serge-scl/mini-keyboard/part/wheell_z2_2.FCStd

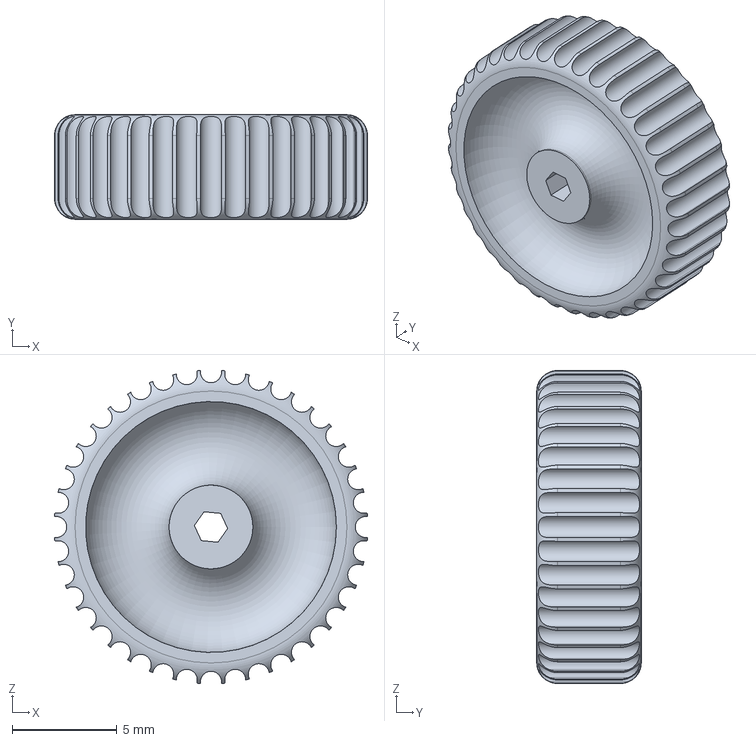
[picture p18: CAD file, 2025-04-07]
part/wheell_z2_2.FCStd
15.0 x 5.00 x 15.0 mm
