serge-scl/mini-keyboard/assembly/plug_front_conn.FCStd

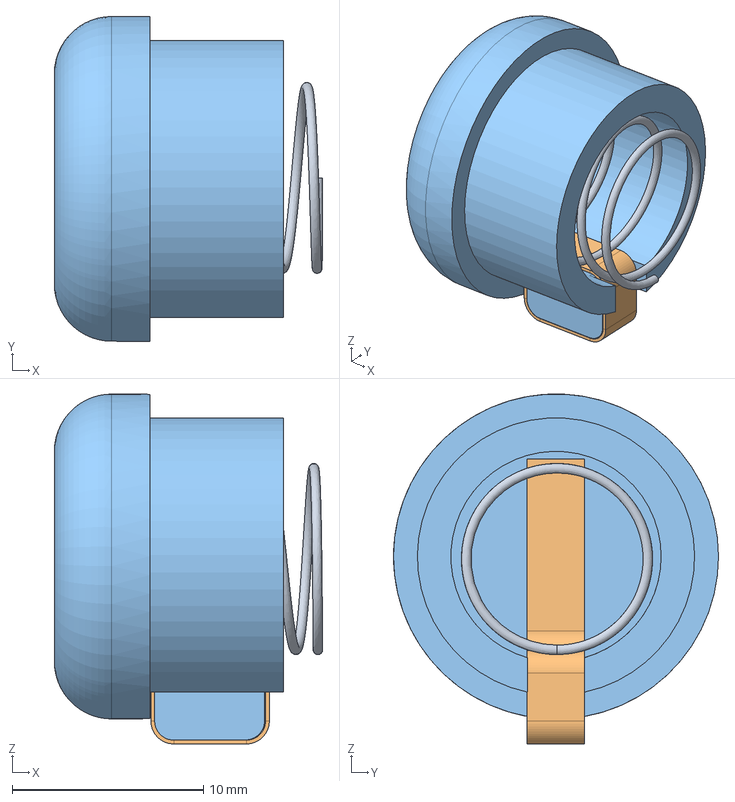
[picture p19: CAD file, 2025-04-07]
assembly/plug_front_conn.FCStd
14.0 x 17.0 x 18.3 mm
spring_battr_001
batr_conn_min_001
plug_front_001
