serge-scl/mini-keyboard/part/steel_ring.FCStd

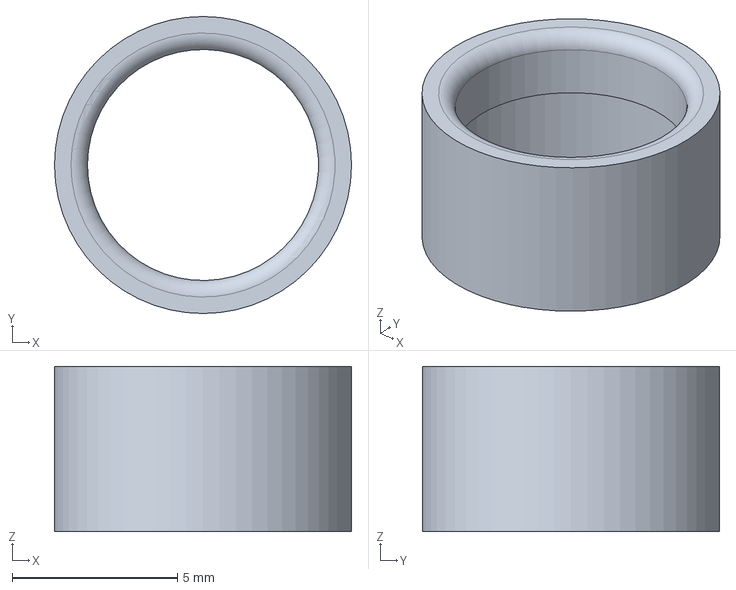
[picture p20: CAD file, 2025-04-07]
part/steel_ring.FCStd
9.00 x 9.00 x 5.00 mm
