serge-scl/mini-keyboard/part/plug_back.FCStd

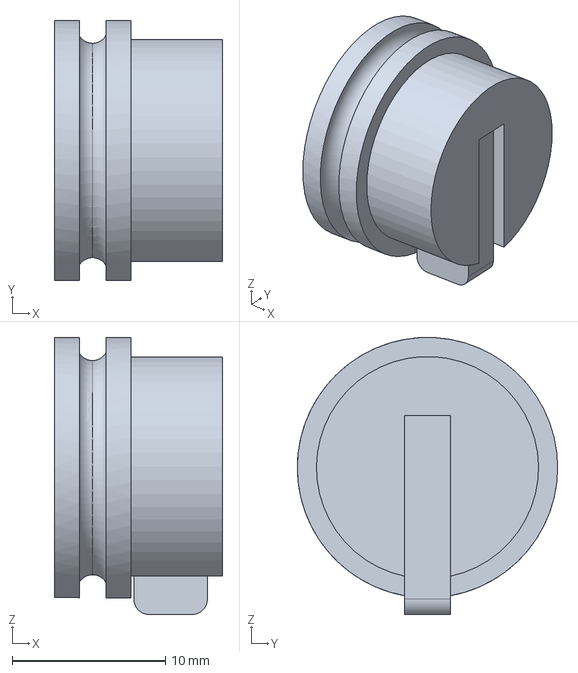
[picture p21: CAD file, 2025-04-07]
part/plug_back.FCStd
11.0 x 17.0 x 18.1 mm
