serge-scl/mini-keyboard/assembly/mouse_keyboard_pyramids2.FCStd

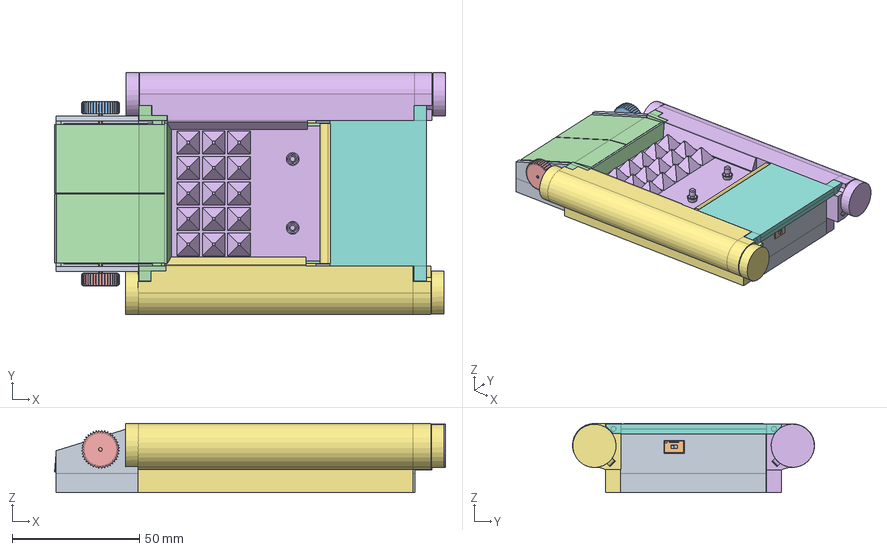
[picture p22: CAD file, 2025-02-04]
assembly/mouse_keyboard_pyramids2.FCStd
153.5 x 95.0 x 27.2 mm
bottom_001
lens_001
fixing_pin_001
fixing_pin_002
fixing_pin_003
fixing_pin_004
back_lock_001
back_cover_stock_001
Raspberry_pi_Pico_001
mouse_wheel_axis_001
wheell_z2_2_001
axle_tube_case_001
wheell_z2_2_002
battery_wall_right_asm_001
battery_wall_left_asm_001
tch_btm_conn_001
mov_kb_block_001
mov_joystick_block_001
mov_joystick_block_002
button_mechanism_001
kbrd_sheet_screen_001
pyramids_001
Pcb_469f
${REFERENCE}_R_0603_1608Metric_null x 8
${REFERENCE}_TO-92S_null x 6
${REFERENCE}_CP_EIA_1608_08_AVX_J_null x 12
Lead
Lead001
Lead002
Lead003
Lead004
Lead005
Lead006
Lead007
Lead(Mirror)
Lead(Mirror)001
Lead(Mirror)002
Lead(Mirror)003
Lead(Mirror)004
Lead(Mirror)005
Lead(Mirror)006
Lead(Mirror)007
body_swetch2_001 x 3
button_switch1_001 x 3
button_conn1_001 x 3
${REFERENCE}_CP_EIA_3216_12_Kemet_S_null x 2
encoder2_001
brake_well1_001
terminal1_001
base1_001
${REFERENCE}_SOT_23_5_null
${REFERENCE}_R_0402_1005Metric_null x 2
${REFERENCE}_Cylinder_null
${REFERENCE}_D_SOD_523_null x 29
BF088-10-A-L-D_H x 2
BF088-10-A-L-D_P x 2
BF088-10-A-L-D_P001 x 2
BF088-10-A-L-D_P002 x 2
BF088-10-A-L-D_P003 x 2
BF088-10-A-L-D_P004 x 2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
