serge-scl/mini-keyboard/part/boll_tilt.FCStd

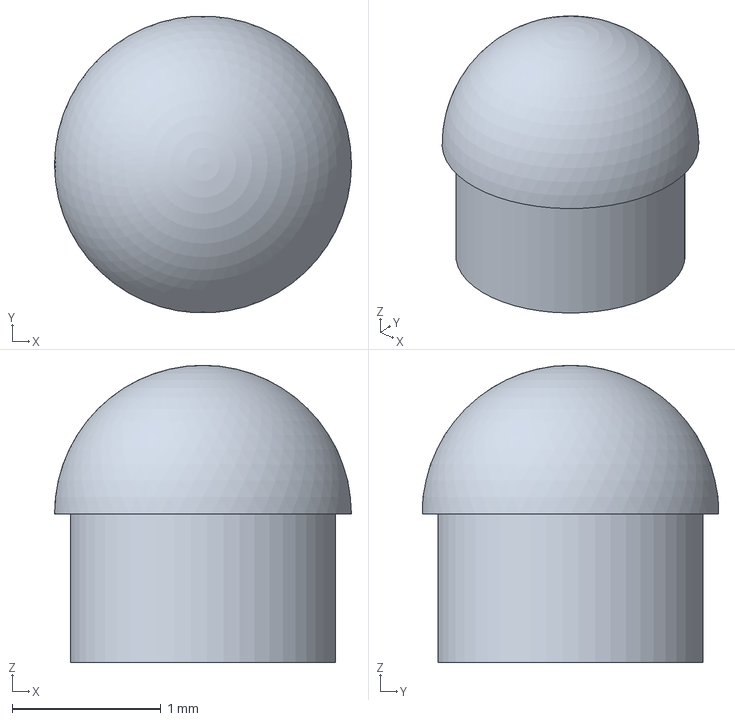
[picture p23: CAD file, 2025-04-07]
part/boll_tilt.FCStd
2.00 x 2.00 x 2.00 mm
