serge-scl/mini-keyboard/assembly/tch_btm_conn.FCStd

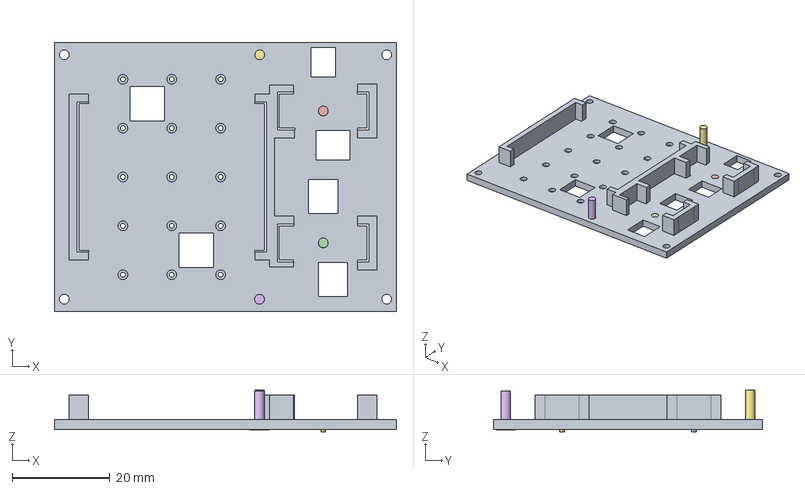
[picture p24: CAD file, 2024-12-29]
assembly/tch_btm_conn.FCStd
70.0 x 55.0 x 8.50 mm
touch_bottom2_001
pewter_foot1_002
pewter_foot1_003
pewter_foot2_002
pewter_foot2_003
fix_m_001
fix_m_002
