serge-scl/mini-keyboard/part/LED_D1.8mm_W3.3mm_H2.4mm.step

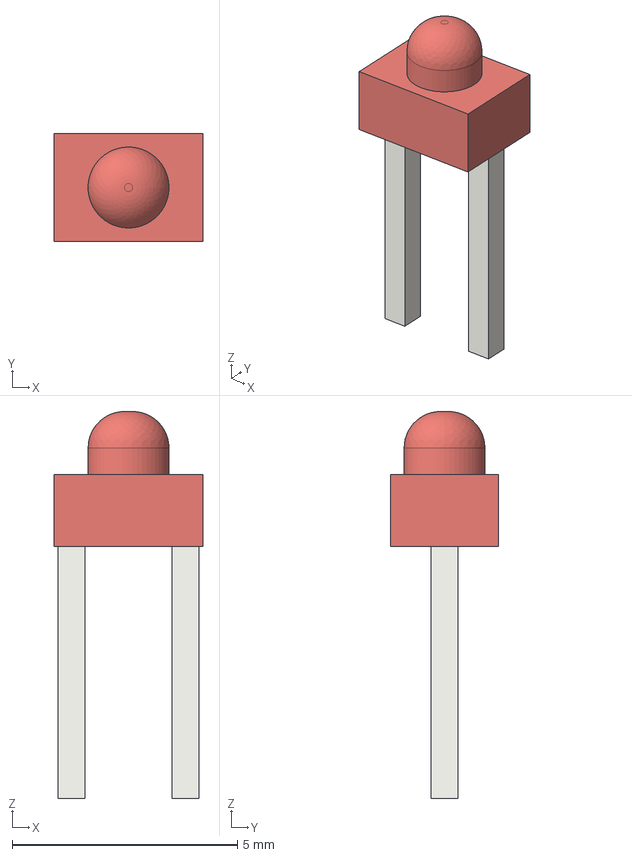
[picture p25: CAD file, 2025-04-07]
part/LED_D1.8mm_W3.3mm_H2.4mm.step
3.30 x 2.40 x 8.60 mm
