serge-scl/mini-keyboard/part/sliding_cell.FCStd

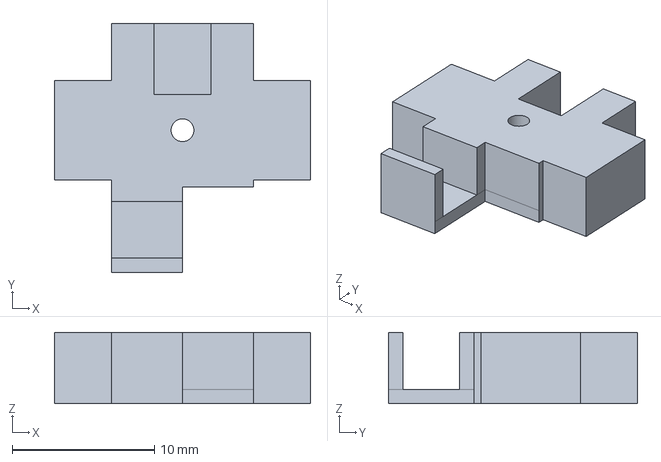
[picture p26: CAD file, 2025-04-07]
part/sliding_cell.FCStd
18.0 x 17.5 x 5.00 mm
