serge-scl/mini-keyboard/assembly/button_mechanism.FCStd

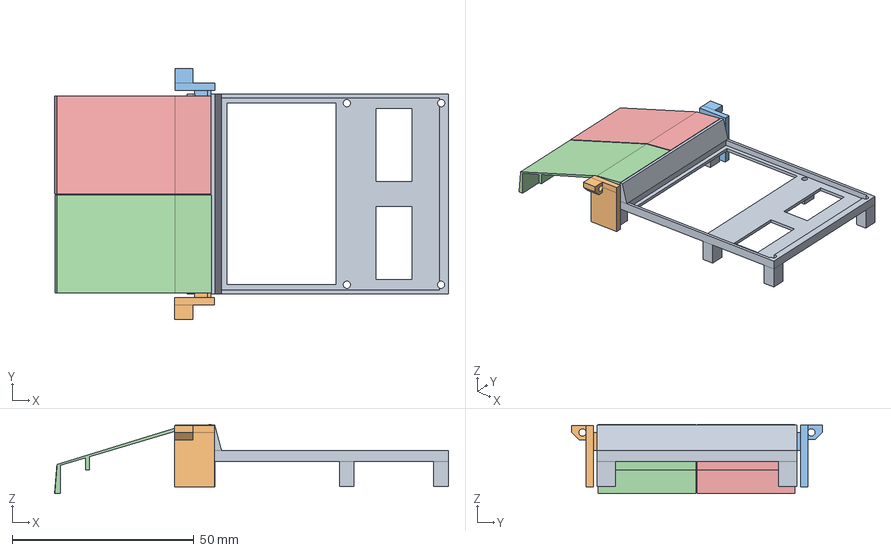
[picture p27: CAD file, 2024-12-02]
assembly/button_mechanism.FCStd
108.5 x 69.1 x 19.0 mm
skelet_bench_001
fix_ring_left_001
fix_ring_rght_001
mouse_button_left_001
mouse_button_right_001
