serge-scl/mini-keyboard/assembly/magnet_with_holder.FCStd

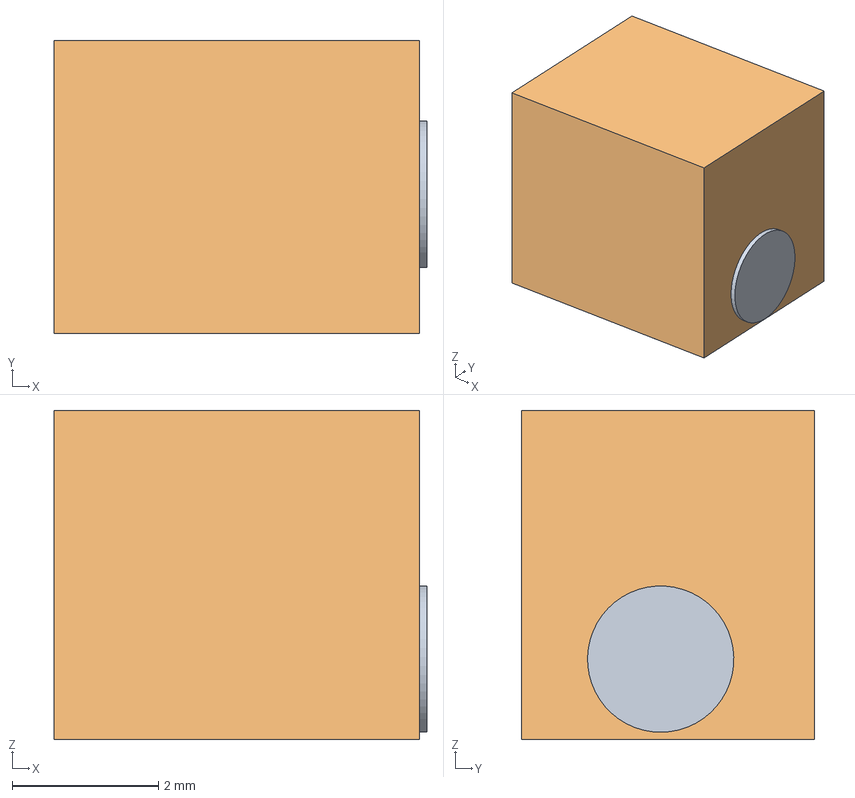
[picture p28: CAD file, 2023-12-05]
assembly/magnet_with_holder.FCStd
5.10 x 4.00 x 4.50 mm
magnet_001
magnet_holder_001
