serge-scl/mini-keyboard/assembly/back_cover_stock.FCStd

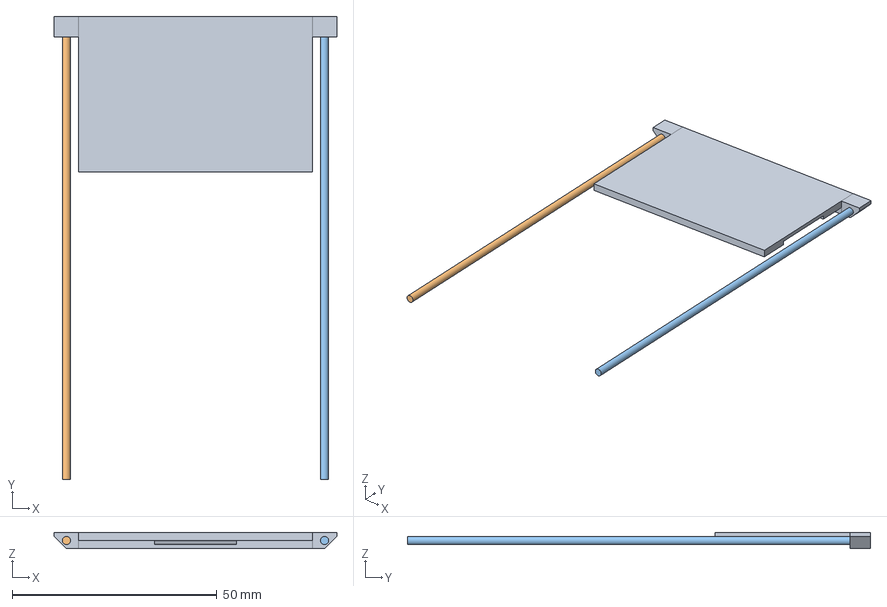
[picture p29: CAD file, 2023-08-21]
assembly/back_cover_stock.FCStd
69.0 x 113.0 x 4.00 mm
back_cover_001
stock_001
stock_002
