serge-scl/mini-keyboard/part/rod_shell_foot.FCStd

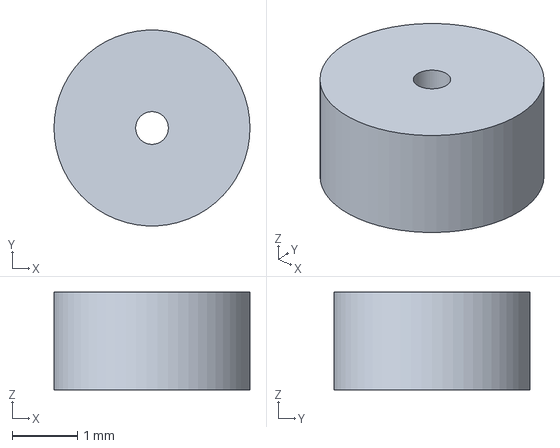
[picture p30: CAD file, 2025-02-23]
part/rod_shell_foot.FCStd
3.00 x 3.00 x 1.50 mm
