serge-scl/mini-keyboard/assembly/mouse_keyboard_pyramids.FCStd

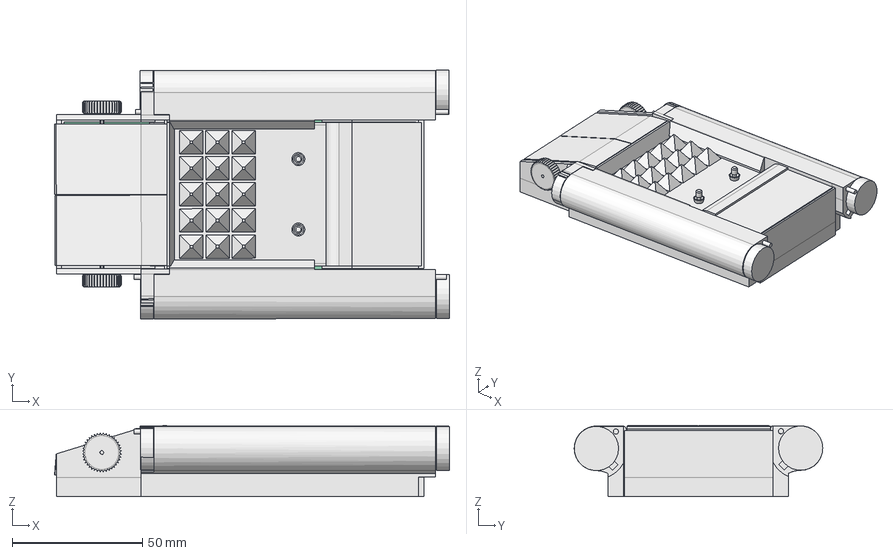
[picture p31: CAD file, 2023-04-01]
assembly/mouse_keyboard_pyramids.FCStd
151.5 x 95.4 x 27.4 mm
Pcb_469f
topPads_469f
botPads_469f
ljtb1_Body_d31762daabe7[2] x 6
Lead
Lead001
Lead002
Lead003
Lead004
Lead005
Lead006
Lead007
Lead(Mirror)
Lead(Mirror)001
Lead(Mirror)002
Lead(Mirror)003
Lead(Mirror)004
Lead(Mirror)005
Lead(Mirror)006
Lead(Mirror)007
body_swetch2_001 x 3
button_switch1_001 x 3
button_conn1_001 x 3
encoder2_001
brake_well1_001
terminal1_001
base1_001
JP2_Cylinder_504290a98abf
U1_Body_1f34f111c063
lens_001
bottom_001
keyboard_module_001
battery_wall_left_001
battery_wall_right_001
back_lock_001
back_cover_001
mouse_wheel_axis_001
wheell_z2_2_001
wheell_z2_3_001
axle_tube_case_001
plug_back_001
plug_back_002
plug_front_001
plug_front_002
stock_001
stock_002
