serge-scl/mini-keyboard/part/rod shell top.FCStd

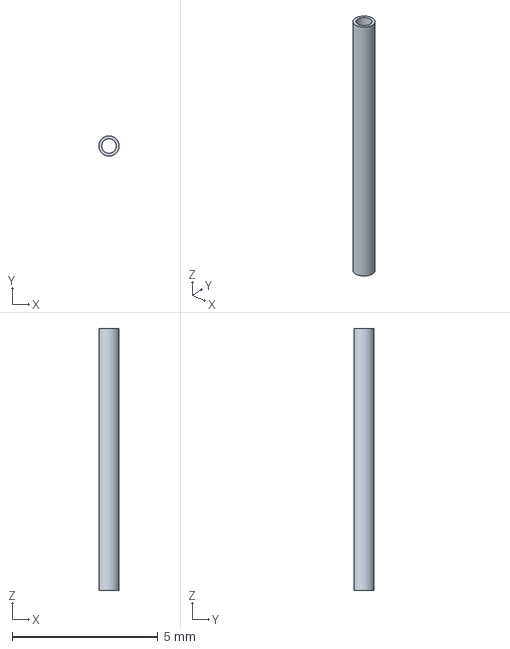
[picture p32: CAD file, 2025-02-23]
part/rod shell top.FCStd
0.699 x 0.7 x 9.00 mm
