serge-scl/mini-keyboard/assembly/Raspberry_pi_Pico.FCStd

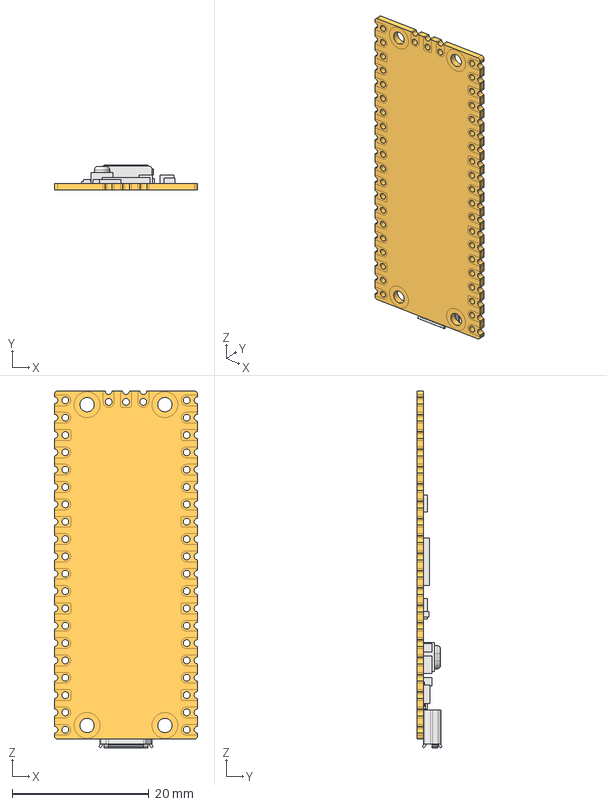
[picture p33: CAD file, 2023-04-01]
assembly/Raspberry_pi_Pico.FCStd
21.0 x 3.73 x 52.3 mm
PICO_REF_BOARD.STEP
PICO_REF_USB.STEP
PICO_REF_USB.STEP001
PICO_REF_USB.STEP002
PICO_REF_USB.STEP003
PICO_REF_USB.STEP004
PICO_REF_SWITCH.STEP
PICO_REF_MICROCONTROLLER.STEP
PICO_REF_LED.STEP
PICO_REF_ONSEMI.STEP
PICO_BOURNS.STEP
PICO_MURATA.STEP
PICO_MURATA.STEP001
PICO_RICHTEK.STEP
PICO_DIODES.STEP
PICO_AEL.STEP
PICO_WINBOND.STEP
