serge-scl/mini-keyboard/part/LED 2835.stp

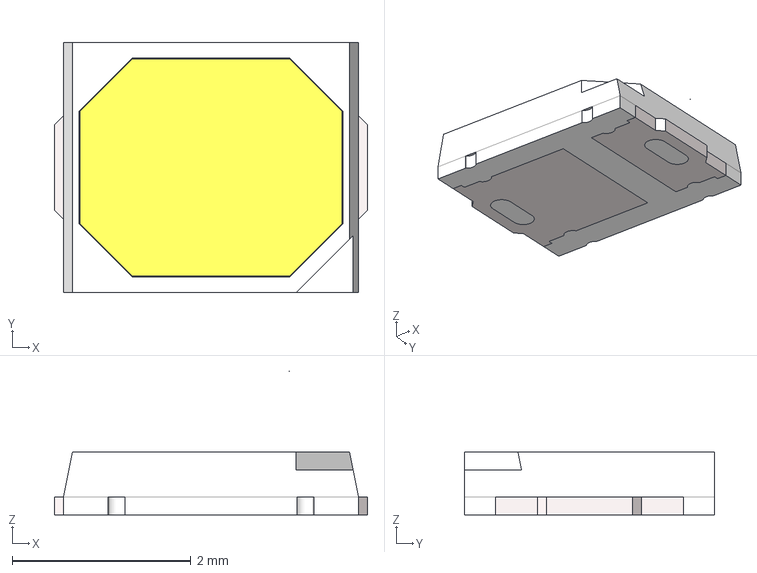
[picture p34: CAD file, 2025-02-23]
part/LED 2835.stp
3.50 x 2.80 x 1.61 mm
