serge-scl/mini-keyboard/part/tip_touch.FCStd

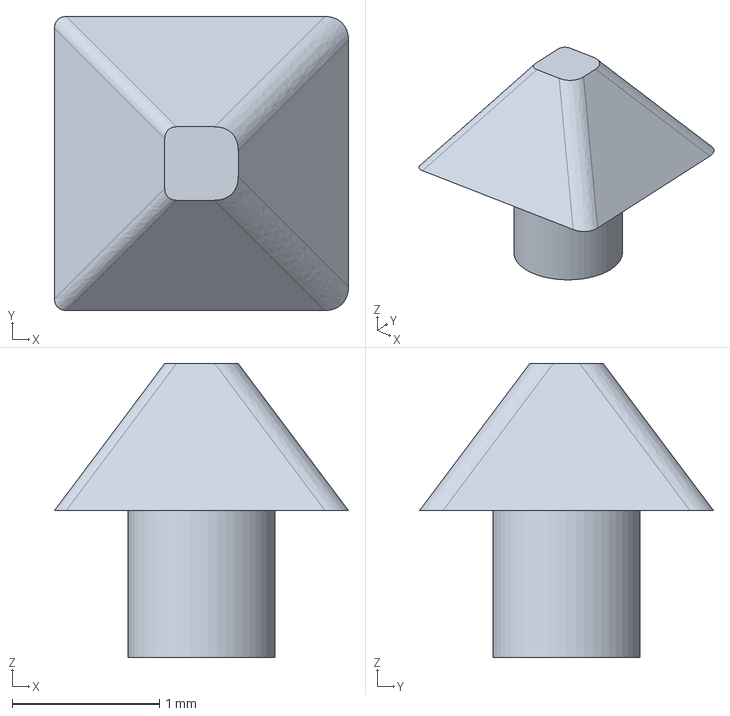
[picture p35: CAD file, 2025-02-23]
part/tip_touch.FCStd
2.00 x 2.00 x 2.00 mm
