serge-scl/mini-keyboard/part/Joystick.FCStd

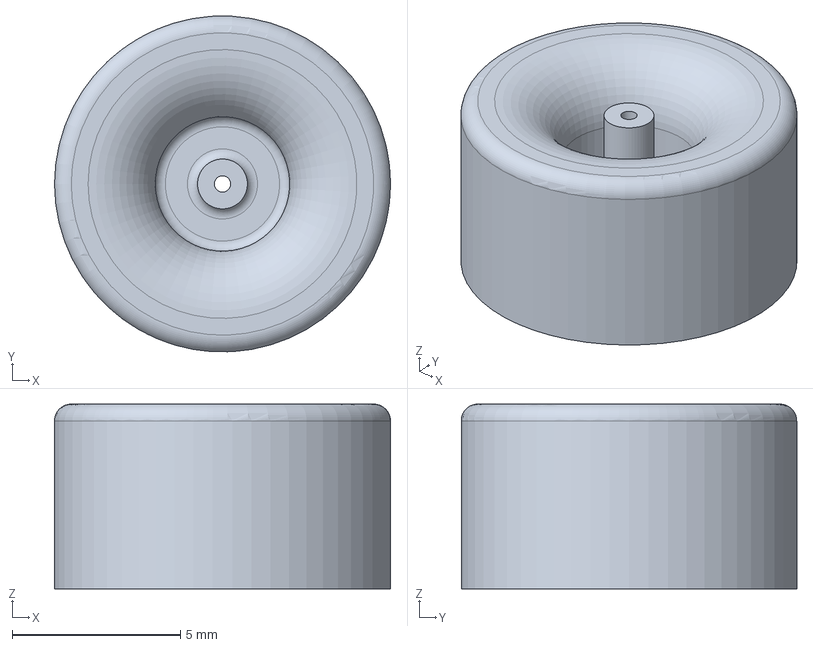
[picture p36: CAD file, 2025-02-23]
part/Joystick.FCStd
10.0 x 9.99 x 5.50 mm
