serge-scl/mini-keyboard/part/kbrd_sheet_screen.FCStd

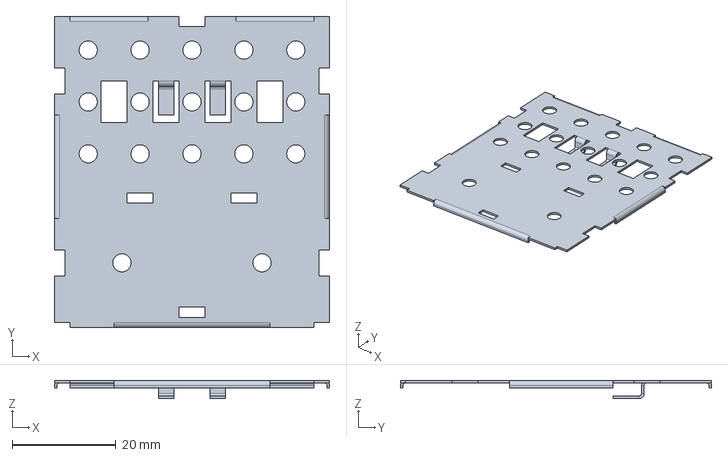
[picture p37: CAD file, 2025-02-23]
part/kbrd_sheet_screen.FCStd
53.0 x 60.0 x 3.50 mm
