serge-scl/mini-keyboard/part/RC0402N_PAN.step

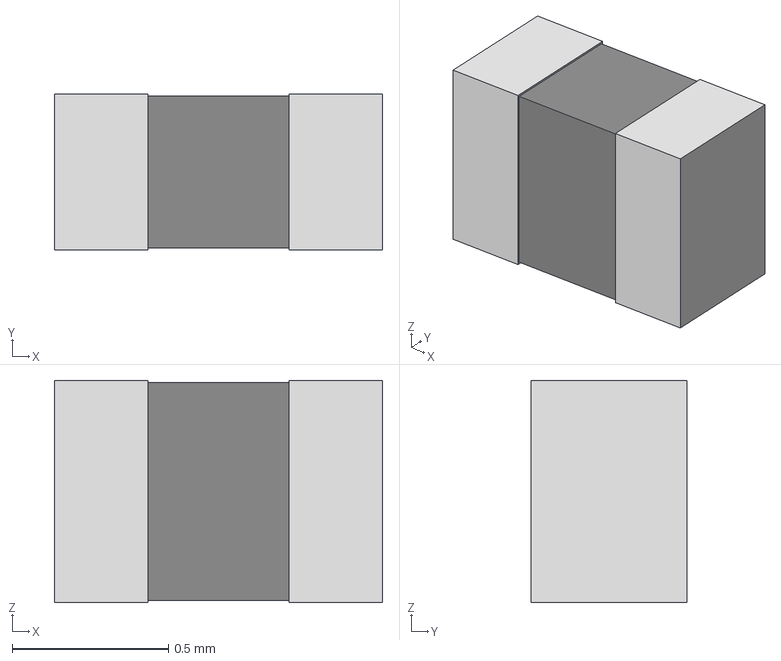
[picture p38: CAD file, 2025-02-04]
part/RC0402N_PAN.step
1.05 x 0.5 x 0.711 mm
