serge-scl/mini-keyboard/part/SDA01H1SBD.step

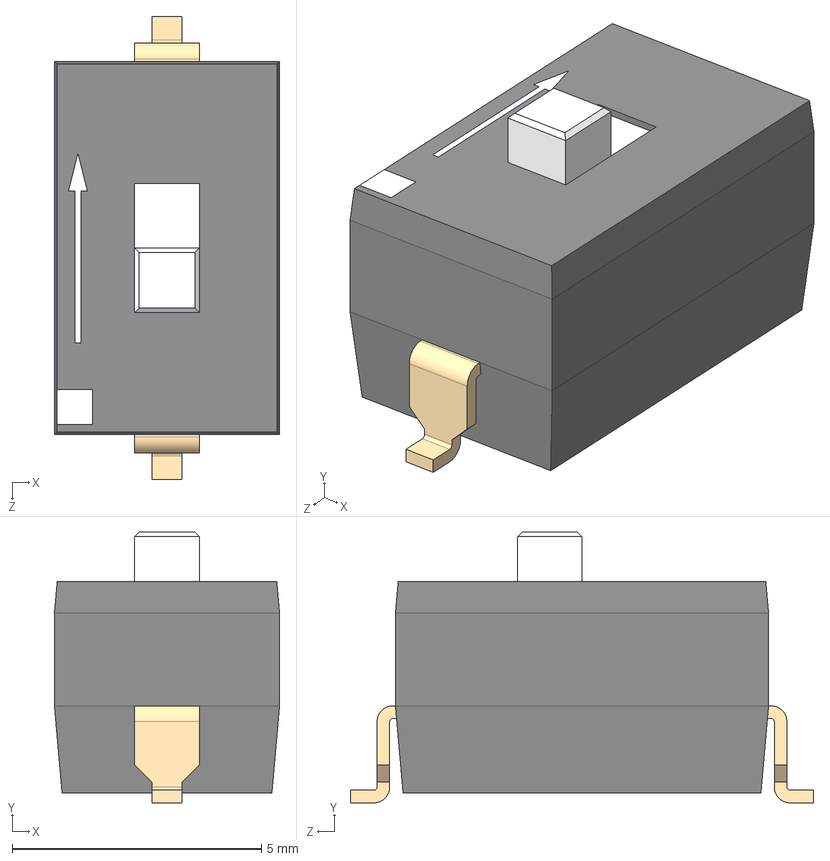
[picture p39: CAD file, 2025-02-01]
part/SDA01H1SBD.step
4.52 x 5.44 x 9.30 mm
