serge-scl/mini-keyboard/part/lens.FCStd

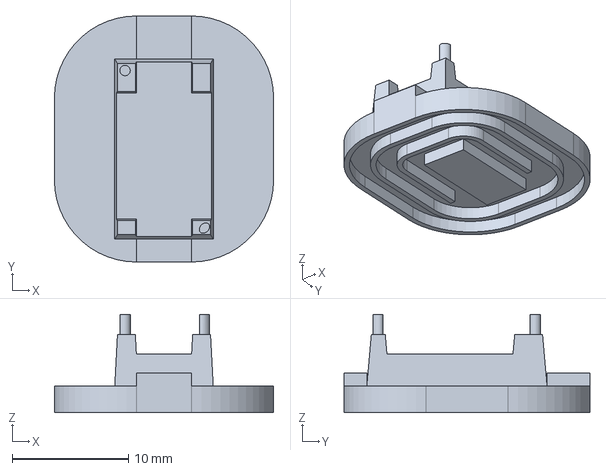
[picture p40: CAD file, 2025-01-19]
part/lens.FCStd
18.9 x 21.1 x 8.46 mm
