serge-scl/mini-keyboard/part/BF020-10-A-B-0300-0200-N-G.stp

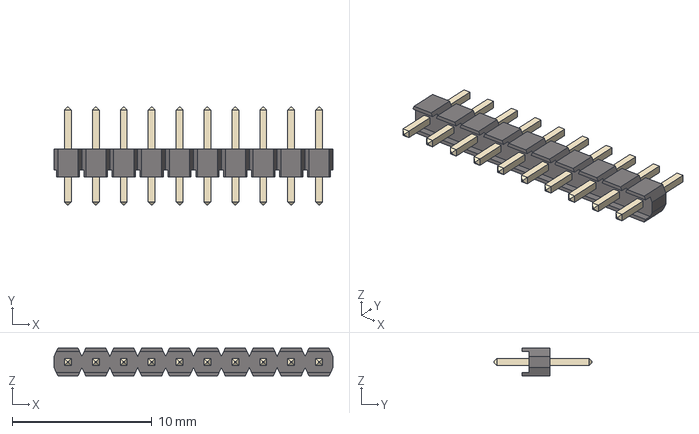
[picture p41: CAD file, 2025-01-13]
part/BF020-10-A-B-0300-0200-N-G.stp
20.0 x 7.00 x 2.00 mm
BF020-10-A-B-0300-0200-N-G_H
BF020-10-A-B-0300-0200-N-G_P x 10
