serge-scl/mini-keyboard/part/BF088-10-A-L-D.stp

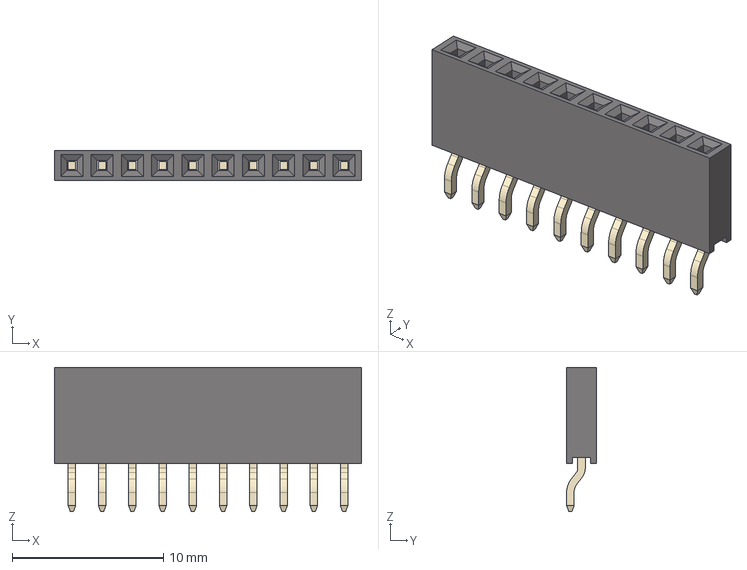
[picture p42: CAD file, 2025-01-13]
part/BF088-10-A-L-D.stp
20.3 x 2.00 x 9.55 mm
BF088-10-A-L-D_H
BF088-10-A-L-D_P x 10
