serge-scl/mini-keyboard/part/BF020-02-A-B-0600-0100-N-G.stp

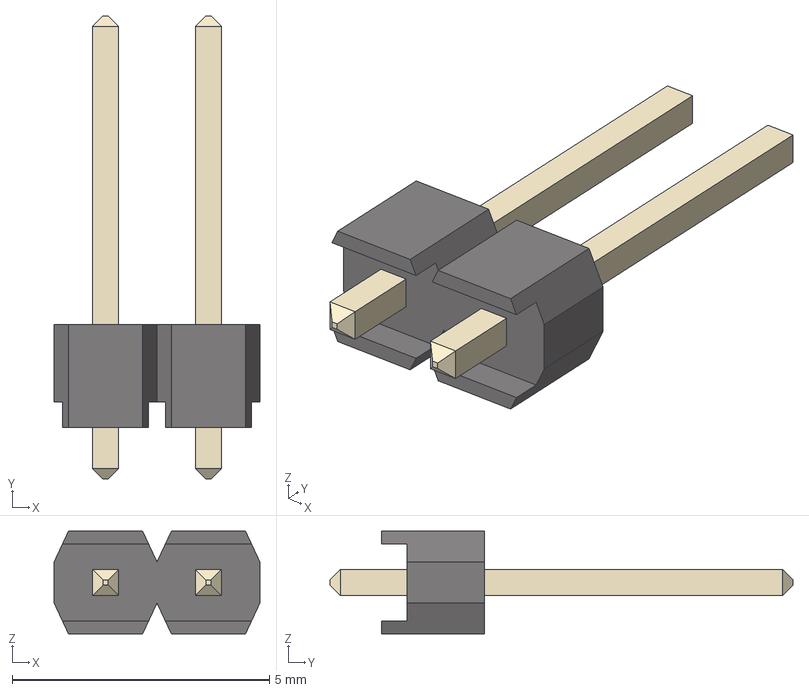
[picture p43: CAD file, 2025-01-09]
part/BF020-02-A-B-0600-0100-N-G.stp
4.00 x 9.00 x 2.00 mm
BF020-02-A-B-0600-0100-N-G_H
BF020-02-A-B-0600-0100-N-G_P x 2
