serge-scl/mini-keyboard/part/BF050-04-A-B-0600-0100-N-G.stp

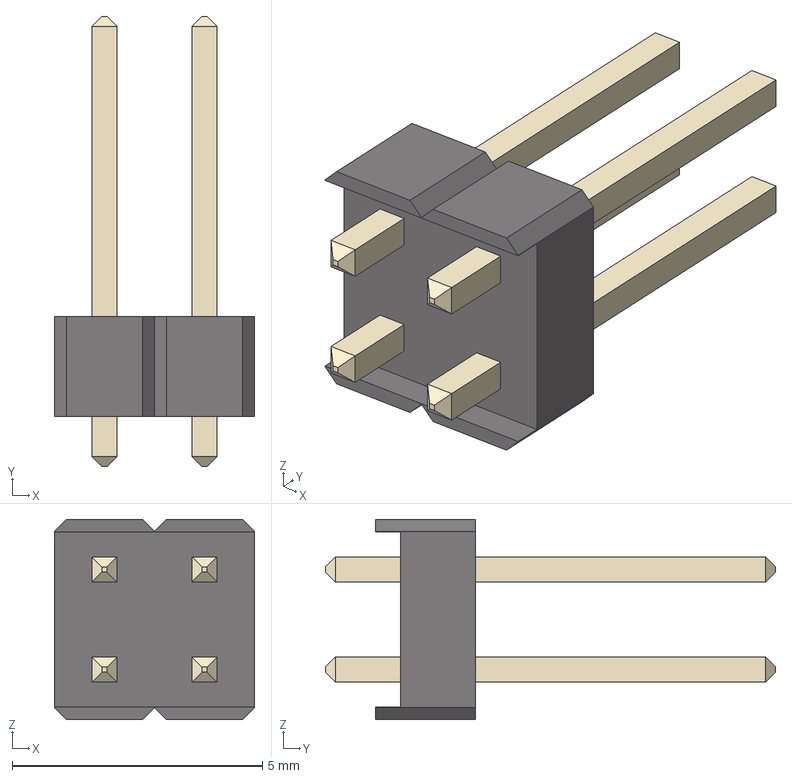
[picture p44: CAD file, 2025-01-09]
part/BF050-04-A-B-0600-0100-N-G.stp
4.00 x 9.00 x 4.00 mm
BF050-04-A-B-0600-0100-N-G_H
BF050-04-A-B-0600-0100-N-G_P x 4
