serge-scl/mini-keyboard/part/D_SOD-123F.step

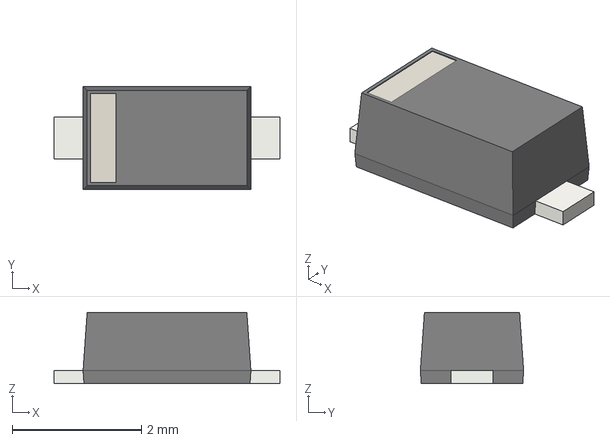
[picture p45: CAD file, 2025-01-09]
part/D_SOD-123F.step
3.50 x 1.60 x 1.10 mm
