serge-scl/mini-keyboard/part/sliding_mesh.FCStd

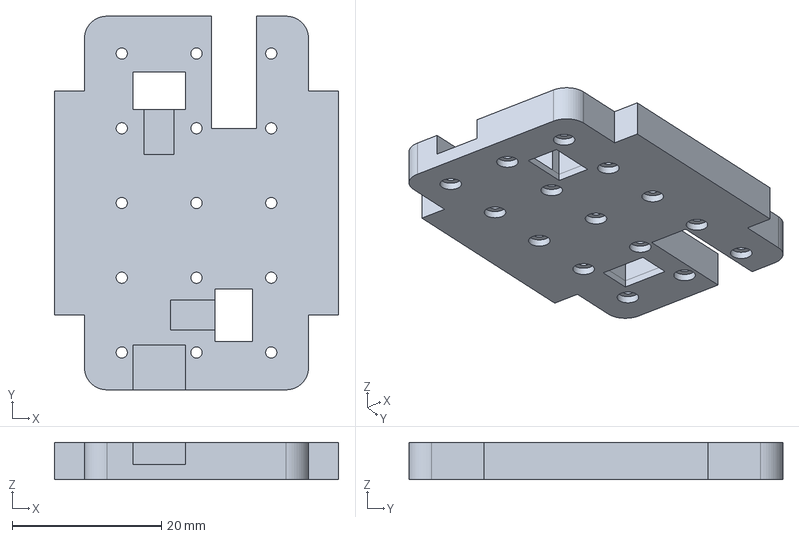
[picture p46: CAD file, 2025-01-05]
part/sliding_mesh.FCStd
38.0 x 50.0 x 5.00 mm
