serge-scl/mini-keyboard/part/BF110-04-A-G.stp

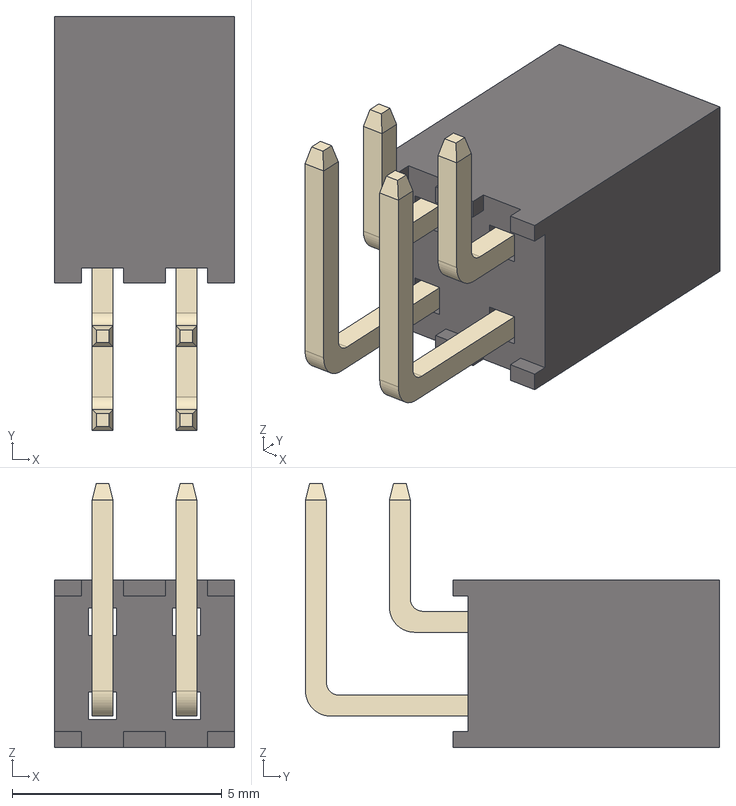
[picture p47: CAD file, 2025-01-05]
part/BF110-04-A-G.stp
4.30 x 9.87 x 6.30 mm
BF110-04-A-G _H
BF110-04-A-G _P1 x 2
BF110-04-A-G _P2 x 2
