serge-scl/mini-keyboard/part/BF086-02-A-0300-N-D.stp

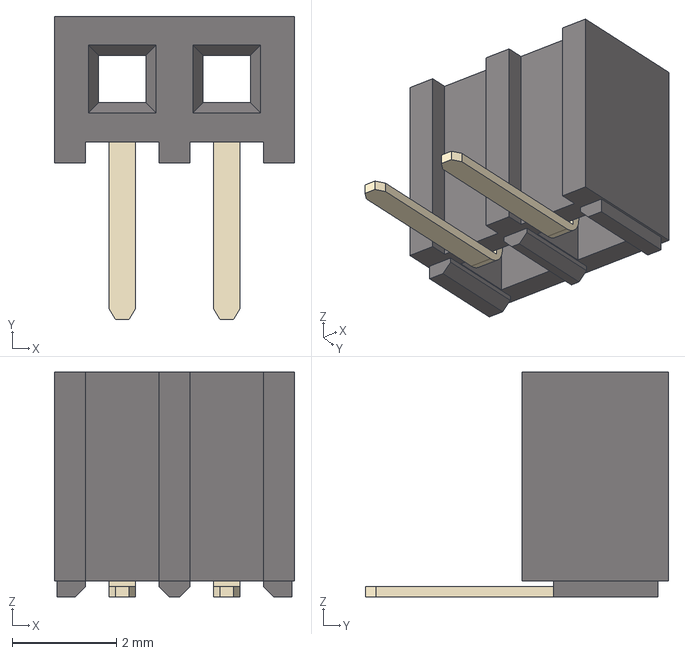
[picture p48: CAD file, 2025-01-05]
part/BF086-02-A-0300-N-D.stp
4.60 x 5.80 x 4.30 mm
BF086-02-A-0300-N-D_H
BF086-02-A-0300-N-D_P x 2
