serge-scl/mini-keyboard/part/kb_set.FCStd

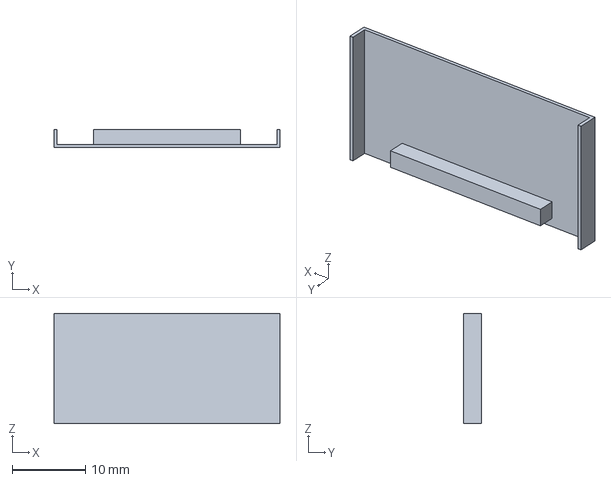
[picture p49: CAD file, 2025-01-05]
part/kb_set.FCStd
30.8 x 2.40 x 15.0 mm
