serge-scl/mini-keyboard/part/fix_ring_rght.FCStd

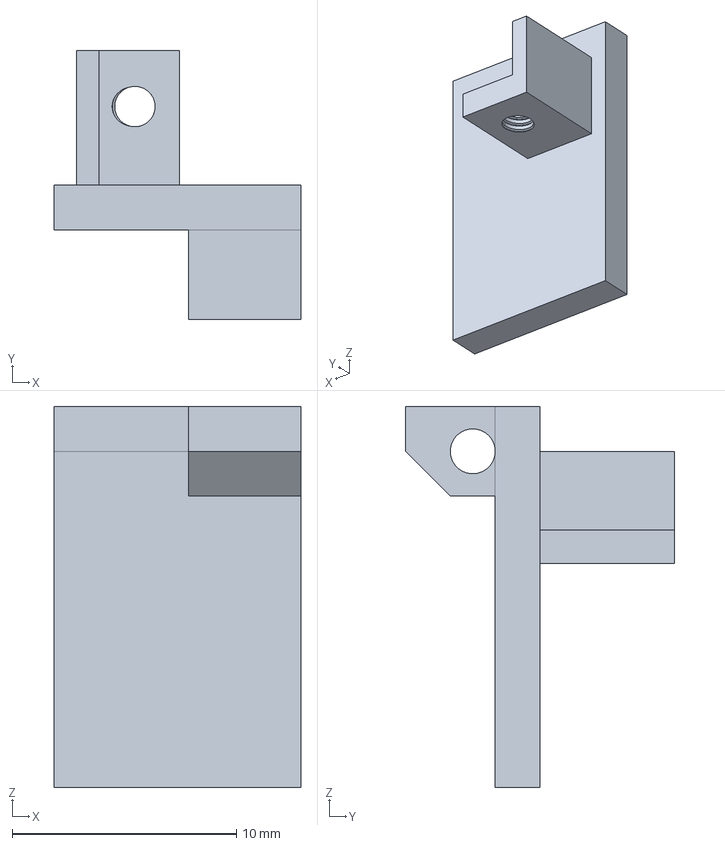
[picture p50: CAD file, 2025-01-05]
part/fix_ring_rght.FCStd
11.0 x 12.0 x 17.0 mm
