serge-scl/mini-keyboard/part/CP_EIA-3216-12_Kemet-S.step

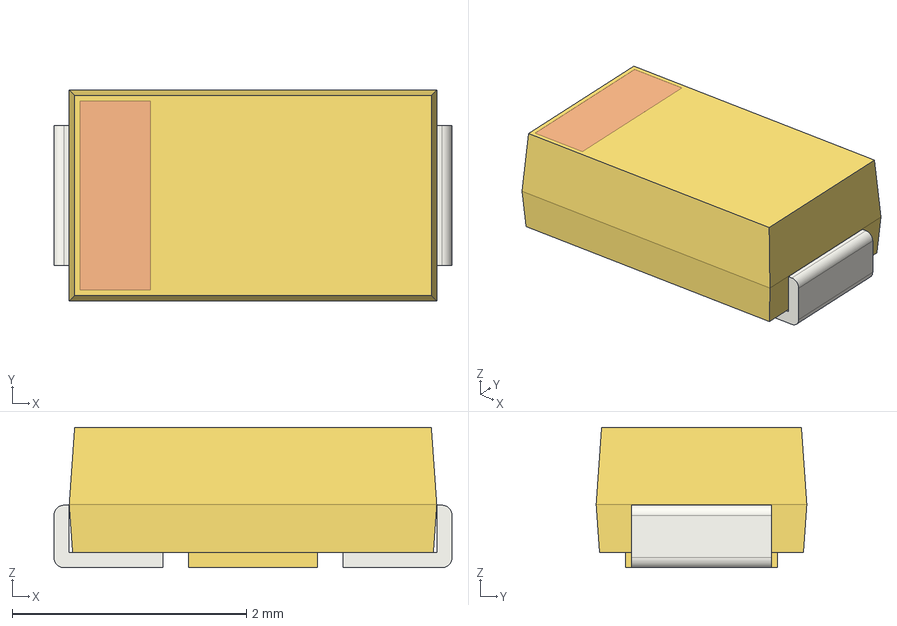
[picture p51: CAD file, 2024-12-29]
part/CP_EIA-3216-12_Kemet-S.step
3.40 x 1.80 x 1.20 mm
