serge-scl/mini-keyboard/part/CP_EIA-3528-12_Kemet-T.step

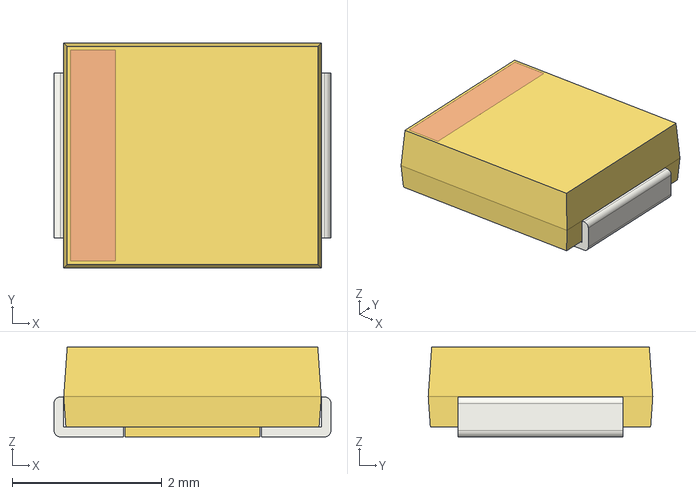
[picture p52: CAD file, 2024-12-29]
part/CP_EIA-3528-12_Kemet-T.step
3.70 x 3.00 x 1.20 mm
