serge-scl/mini-keyboard/part/CP_EIA-1608-08_AVX-J.step

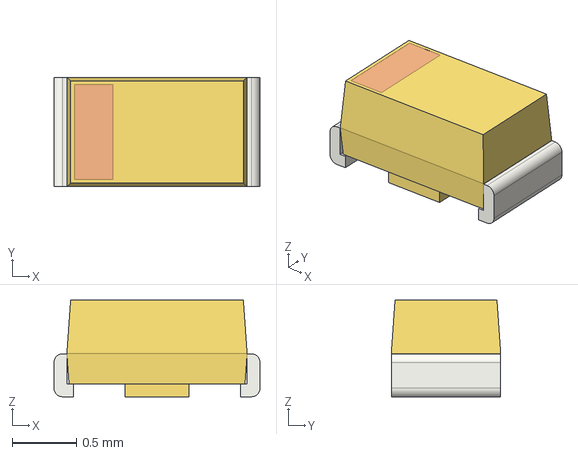
[picture p53: CAD file, 2024-12-29]
part/CP_EIA-1608-08_AVX-J.step
1.60 x 0.85 x 0.75 mm

part/R_0402_1005Metric.step
1.00 x 0.5 x 0.35 mm
