serge-scl/mini-keyboard/part/SOT-23-5.step

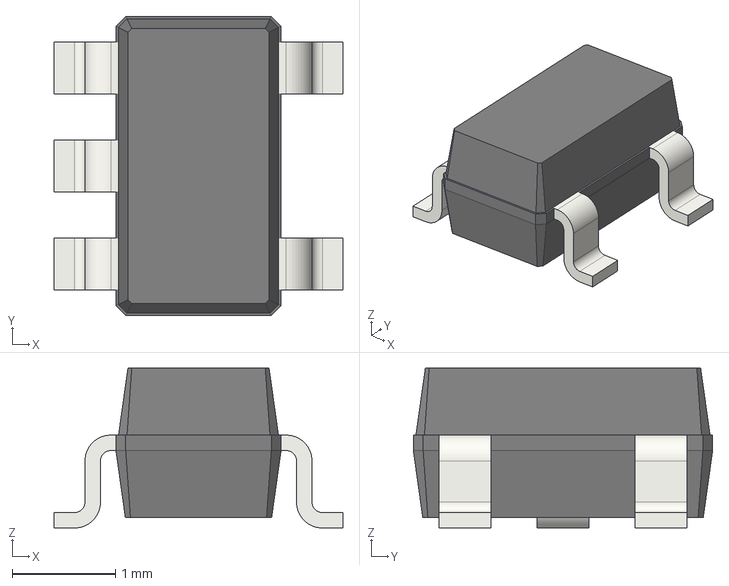
[picture p55: CAD file, 2024-12-24]
part/SOT-23-5.step
2.80 x 2.90 x 1.55 mm
