serge-scl/mini-keyboard/part/TO-92S.step

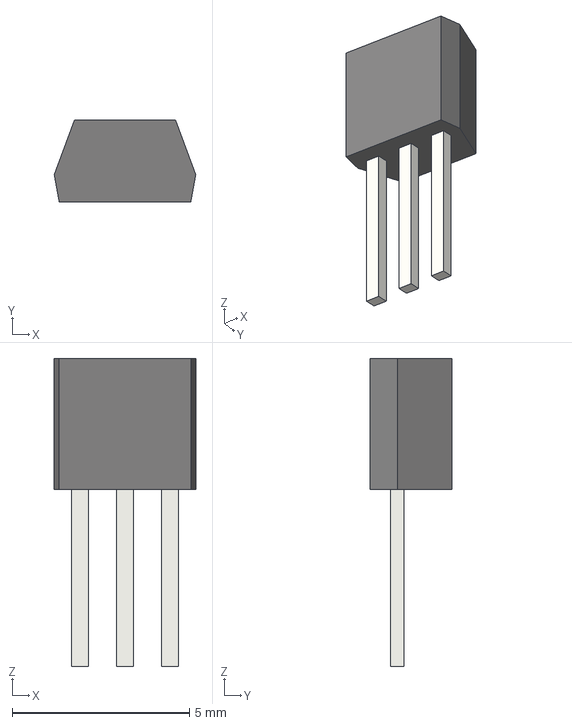
[picture p56: CAD file, 2024-12-24]
part/TO-92S.step
4.00 x 2.31 x 8.70 mm
