serge-scl/mini-keyboard/part/SOT-23.step

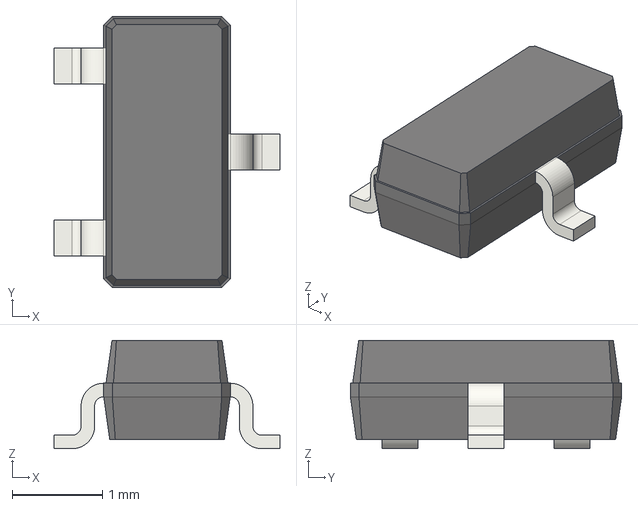
[picture p57: CAD file, 2024-12-24]
part/SOT-23.step
2.50 x 3.00 x 1.20 mm
