serge-scl/mini-keyboard/part/ battery_wall_right.FCStd

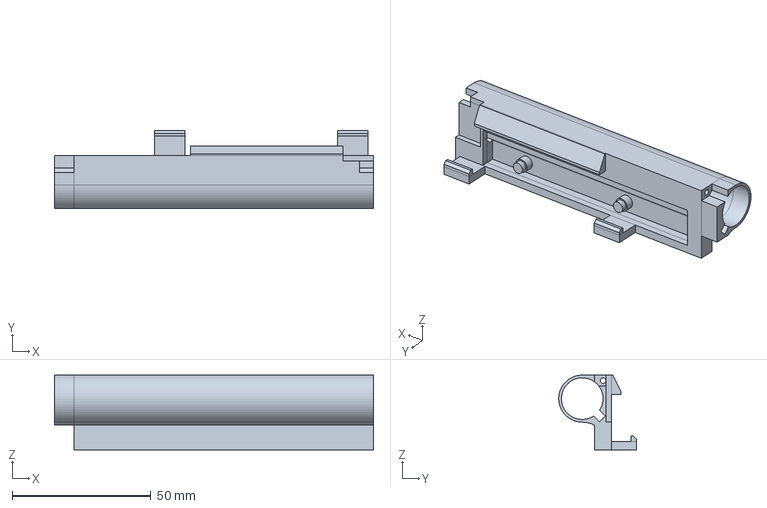
[picture p58: CAD file, 2024-12-24]
part/ battery_wall_right.FCStd
115.0 x 28.0 x 27.0 mm
