serge-scl/mini-keyboard/part/encoder3.step

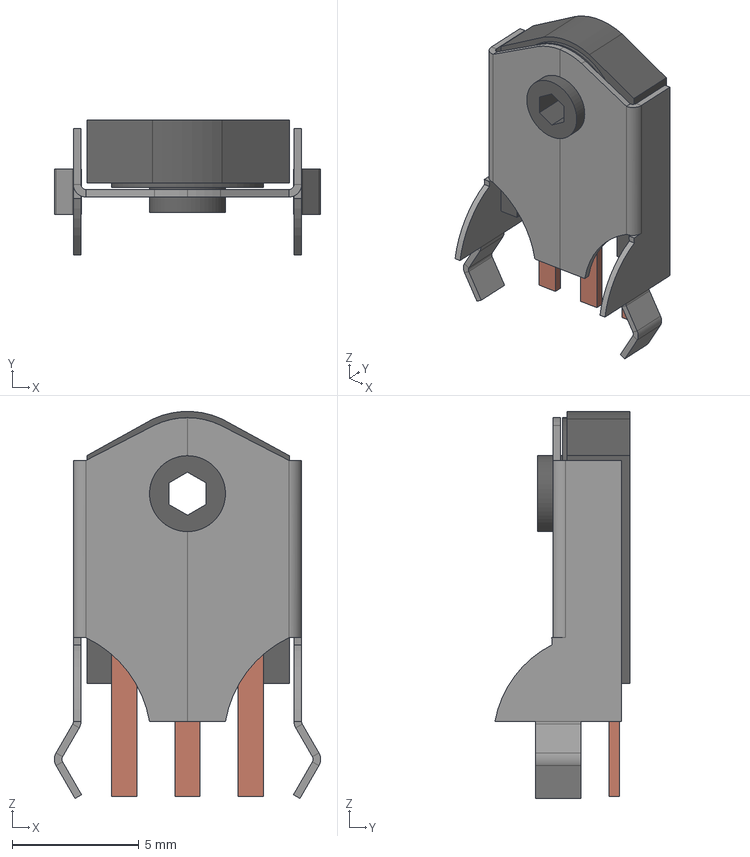
[picture p59: CAD file, 2024-12-24]
part/encoder3.step
10.5 x 5.34 x 15.3 mm
encoder2_001
brake_well1_001
terminal1_001
base1_001
