serge-scl/mini-keyboard/part/D_SOD-523.step

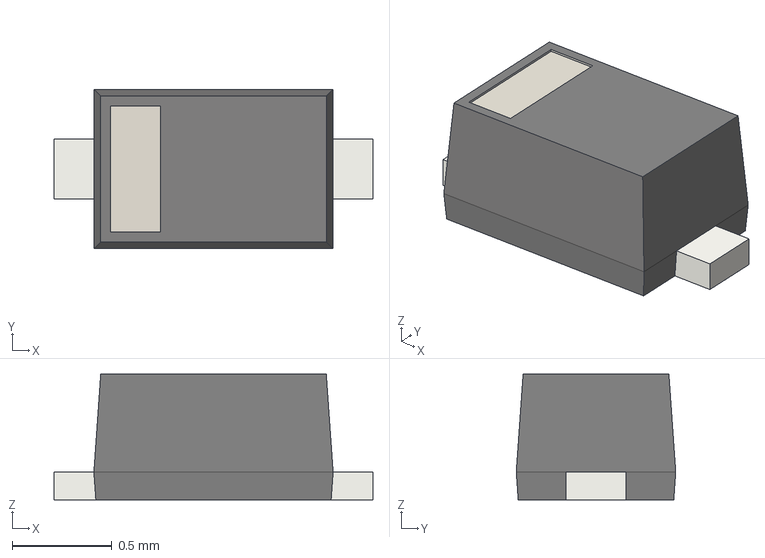
[picture p60: CAD file, 2024-12-24]
part/D_SOD-523.step
1.60 x 0.8 x 0.63 mm
