serge-scl/mini-keyboard/part/mose_switch2.step

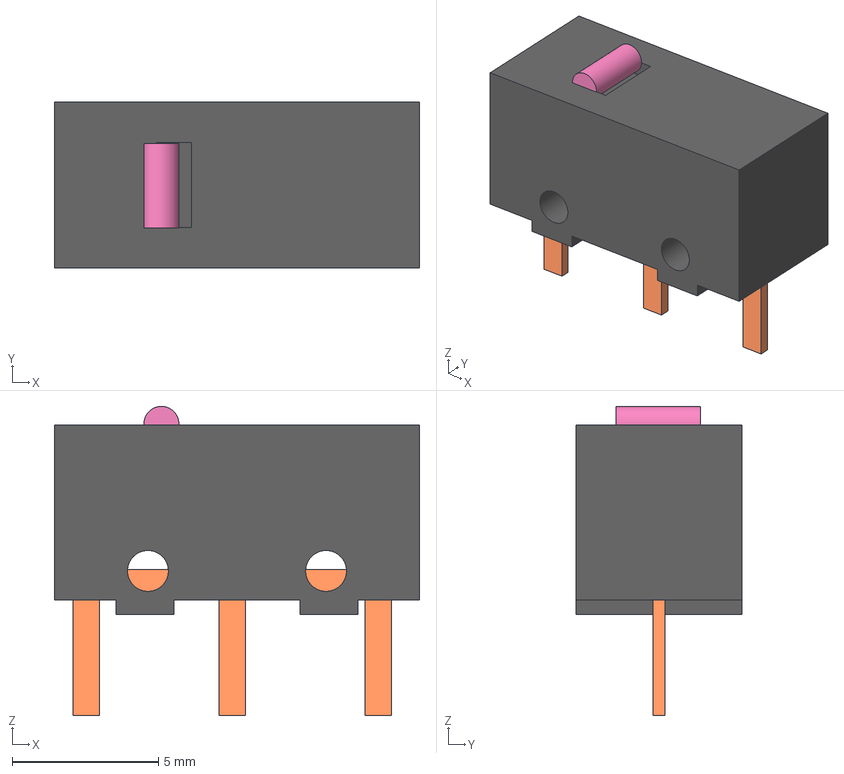
[picture p61: CAD file, 2024-12-24]
part/mose_switch2.step
12.5 x 5.70 x 10.6 mm
body_swetch2_001
button_switch1_001
button_conn1_001
