serge-scl/mini-keyboard/part/R_0603_1608Metric.step

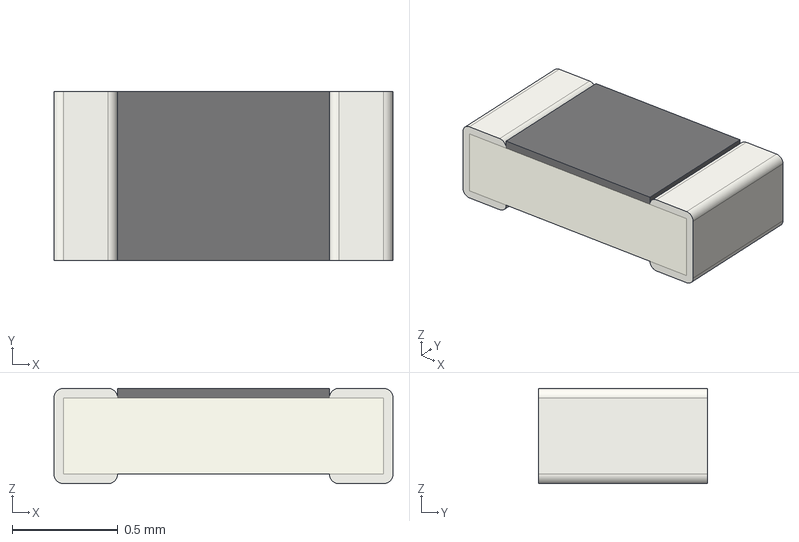
[picture p62: CAD file, 2024-12-24]
part/R_0603_1608Metric.step
1.60 x 0.8 x 0.45 mm
