serge-scl/mini-keyboard/part/SOT-223.step

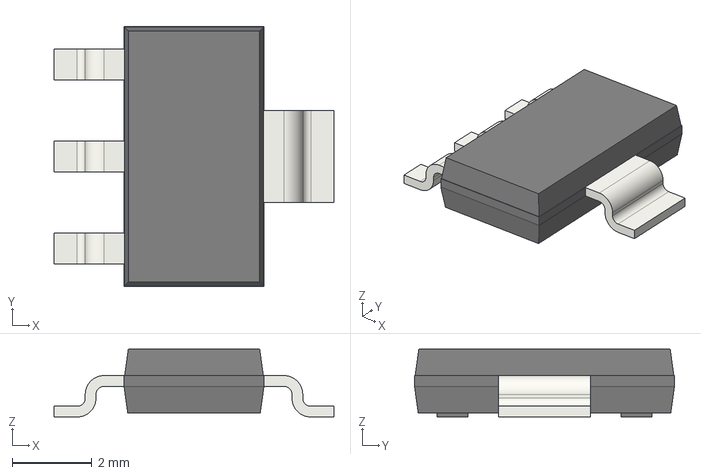
[picture p63: CAD file, 2024-12-24]
part/SOT-223.step
7.00 x 6.50 x 1.70 mm
