serge-scl/mini-keyboard/part/LED_1206_3216Metric_Castellated.step

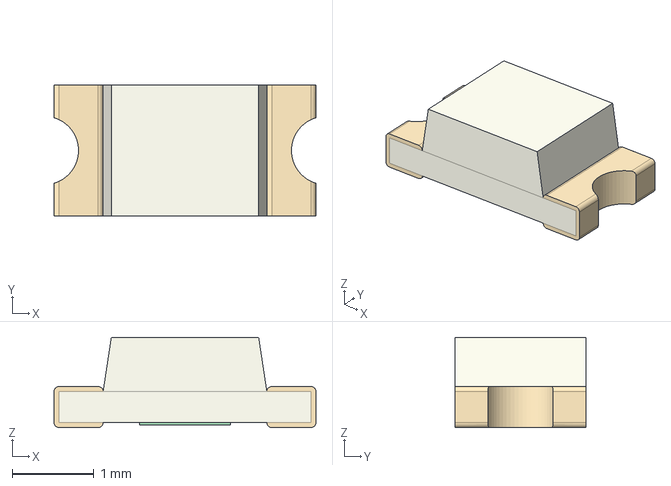
[picture p64: CAD file, 2024-12-24]
part/LED_1206_3216Metric_Castellated.step
3.20 x 1.60 x 1.10 mm
