serge-scl/mini-keyboard/part/pmw3360_chip.step

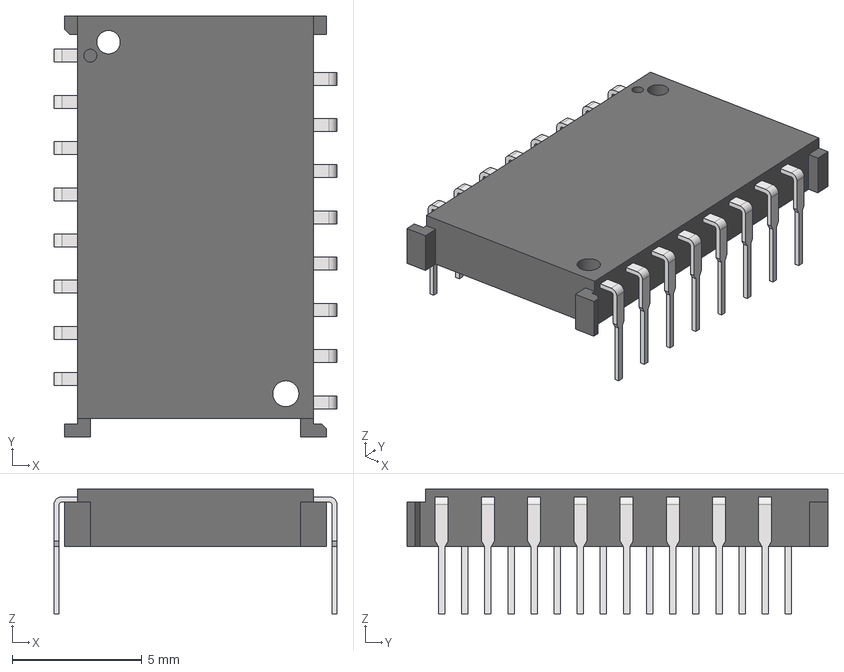
[picture p65: CAD file, 2024-12-24]
part/pmw3360_chip.step
10.9 x 16.2 x 4.81 mm
Lead x 8
Lead(Mirror) x 8
