serge-scl/mini-keyboard/part/UQFN-20-1EP_3x3mm_P0.4mm_EP1.85x1.85mm.step

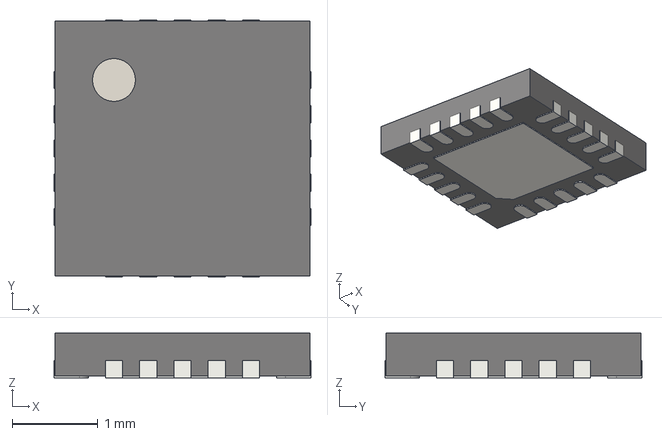
[picture p66: CAD file, 2024-12-24]
part/UQFN-20-1EP_3x3mm_P0.4mm_EP1.85x1.85mm.step
3.00 x 3.00 x 0.52 mm
