serge-scl/mini-keyboard/part/wall_right.FCStd

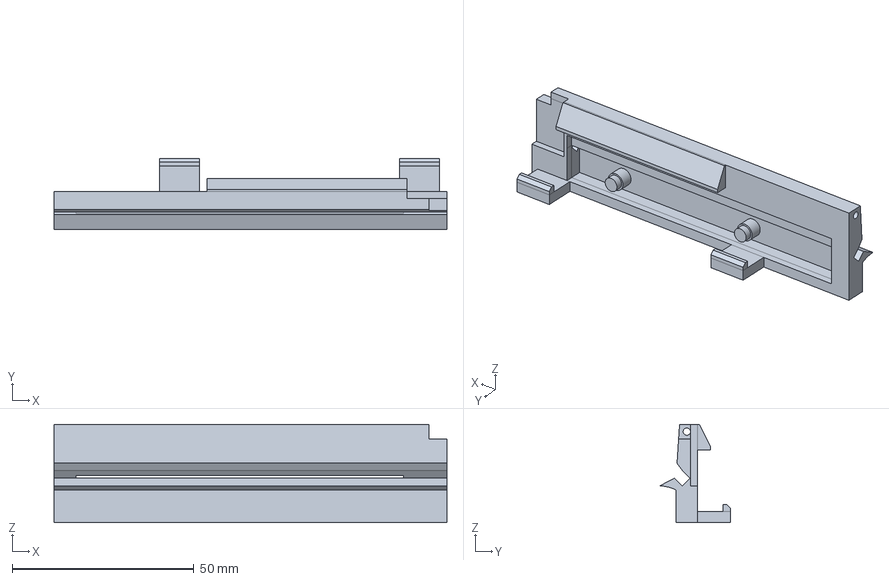
[picture p67: CAD file, 2024-12-18]
part/wall_right.FCStd
108.0 x 19.5 x 27.0 mm
