serge-scl/mini-keyboard/part/batr_conn_pls.FCStd

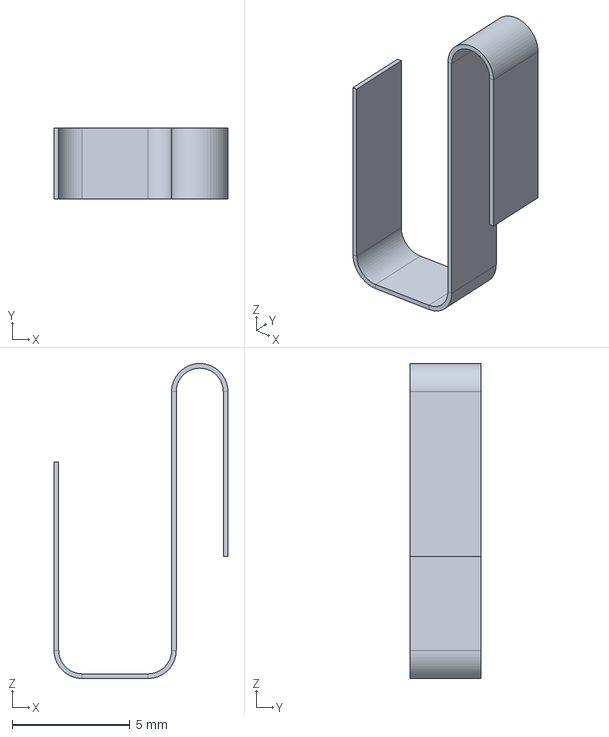
[picture p68: CAD file, 2024-12-18]
part/batr_conn_pls.FCStd
7.40 x 3.00 x 13.4 mm
