serge-scl/mini-keyboard/part/batr_conn_min.FCStd

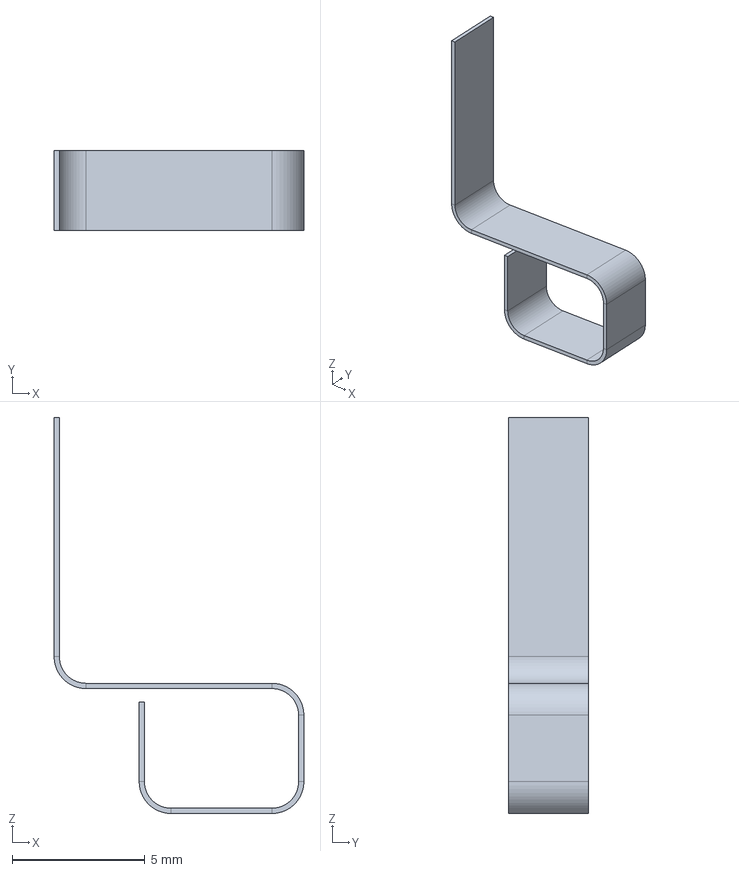
[picture p69: CAD file, 2024-12-18]
part/batr_conn_min.FCStd
9.40 x 3.00 x 14.9 mm
