serge-scl/mini-keyboard/part/pin_conn_btr.FCStd

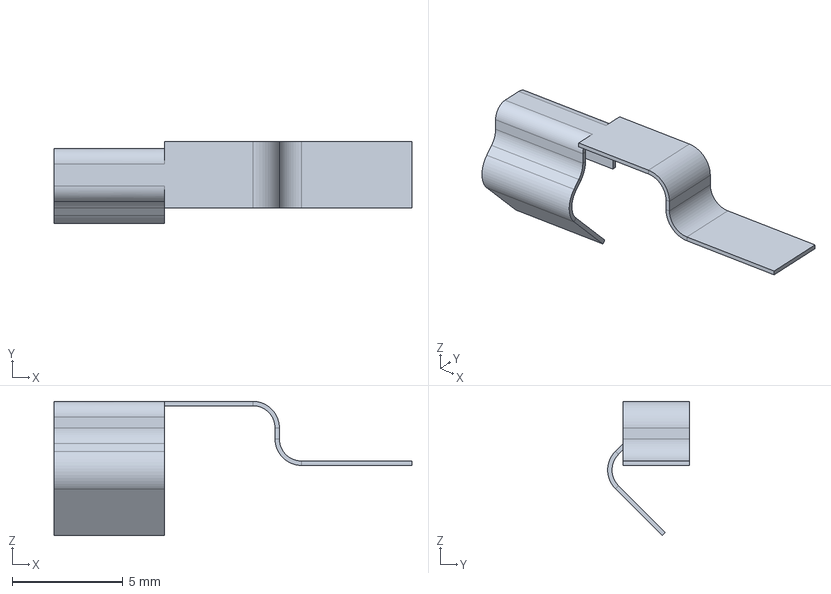
[picture p70: CAD file, 2024-12-18]
part/pin_conn_btr.FCStd
16.2 x 3.70 x 6.08 mm
