serge-scl/mini-keyboard/part/pin_conn_btr2.FCStd

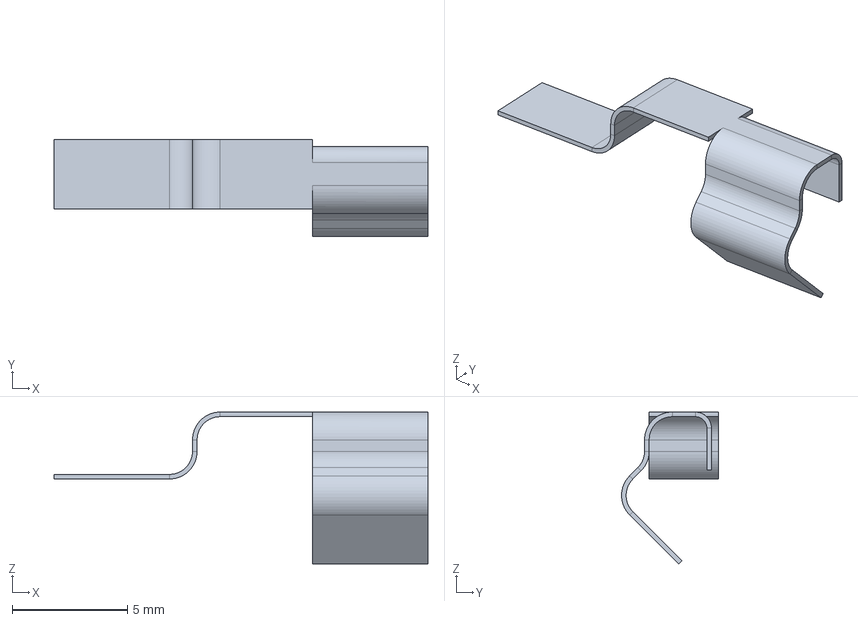
[picture p71: CAD file, 2024-12-18]
part/pin_conn_btr2.FCStd
16.2 x 4.20 x 6.58 mm
