serge-scl/mini-keyboard/part/wall_conn_btr.FCStd

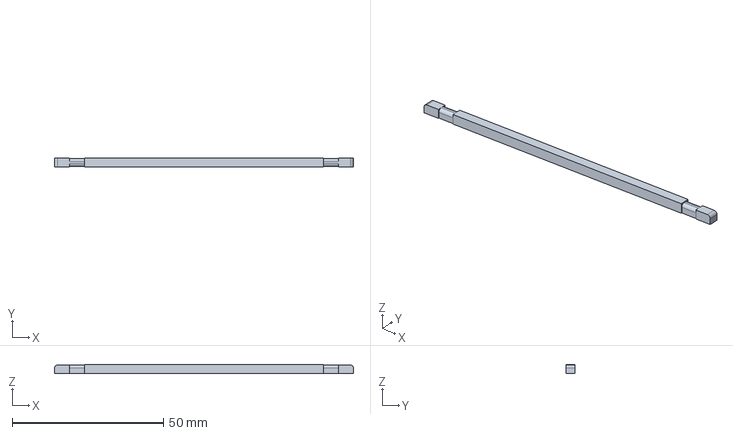
[picture p72: CAD file, 2024-12-18]
part/wall_conn_btr.FCStd
99.0 x 3.00 x 3.00 mm
