serge-scl/mini-keyboard/part/skelet_bench.FCStd

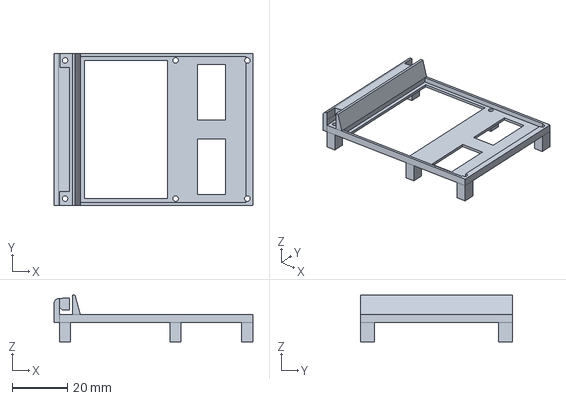
[picture p73: CAD file, 2024-12-02]
part/skelet_bench.FCStd
72.0 x 55.0 x 17.0 mm
