serge-scl/mini-keyboard/part/joyst_set.FCStd

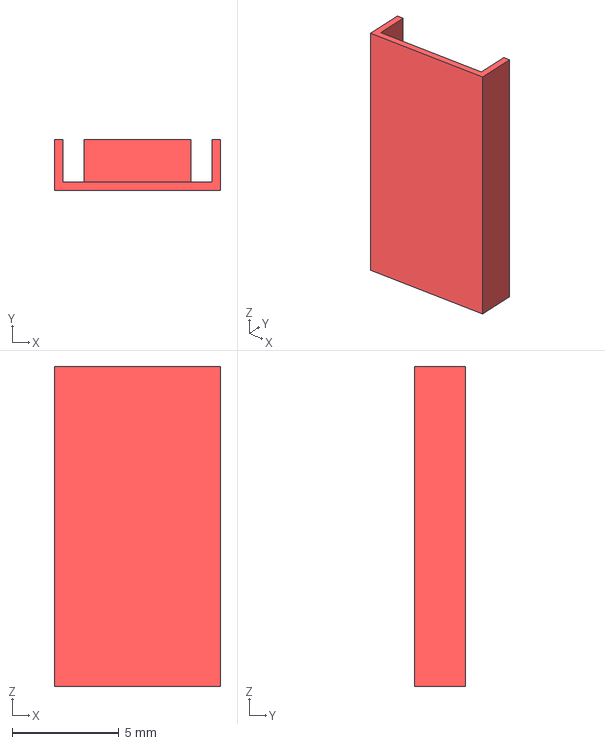
[picture p74: CAD file, 2024-11-11]
part/joyst_set.FCStd
7.80 x 2.40 x 15.0 mm
