serge-scl/mini-keyboard/part/touch_bottom2.FCStd

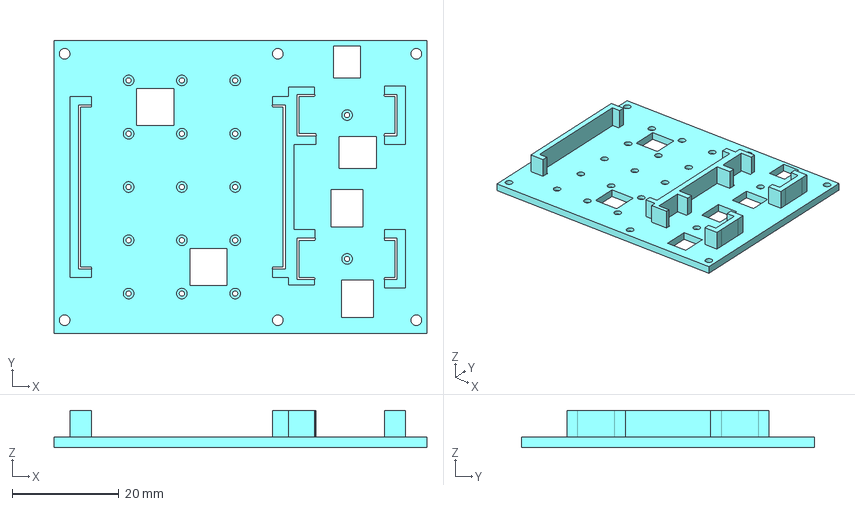
[picture p75: CAD file, 2024-10-30]
part/touch_bottom2.FCStd
70.0 x 55.0 x 7.00 mm
