serge-scl/mini-keyboard/part/fix_m.FCStd

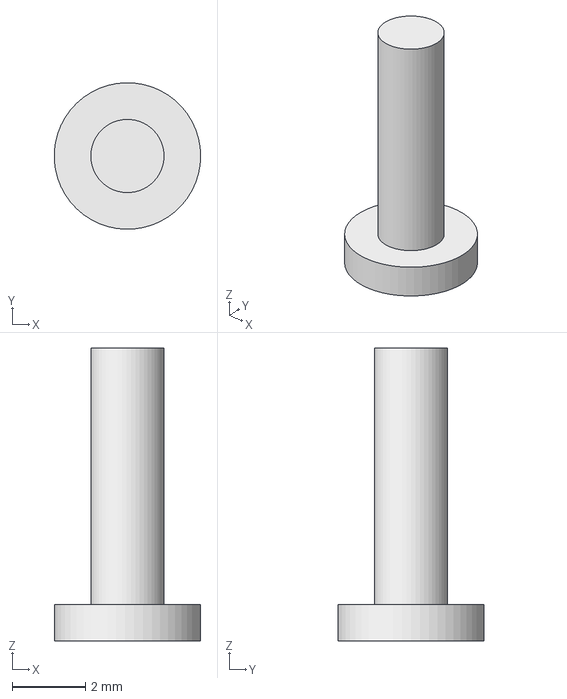
[picture p76: CAD file, 2024-10-30]
part/fix_m.FCStd
4.00 x 4.00 x 8.00 mm
