serge-scl/mini-keyboard/part/spring_battr.FCStd

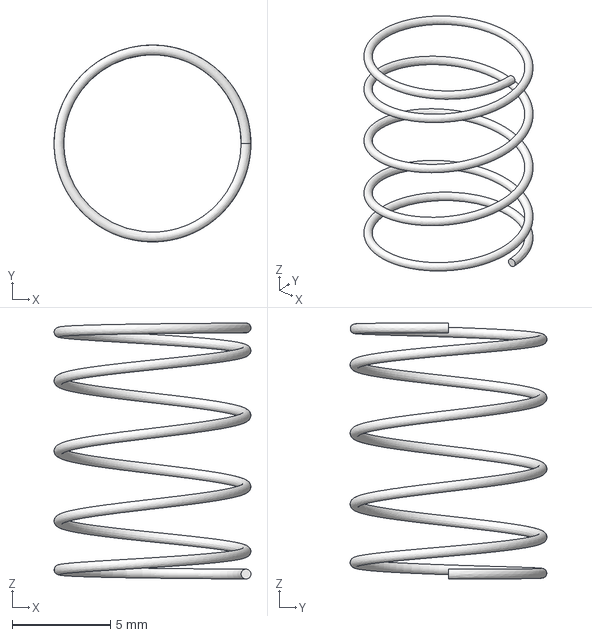
[picture p77: CAD file, 2024-05-27]
part/spring_battr.FCStd
10.00 x 10.0 x 13.0 mm
