serge-scl/mini-keyboard/part/pewter_foot1.FCStd

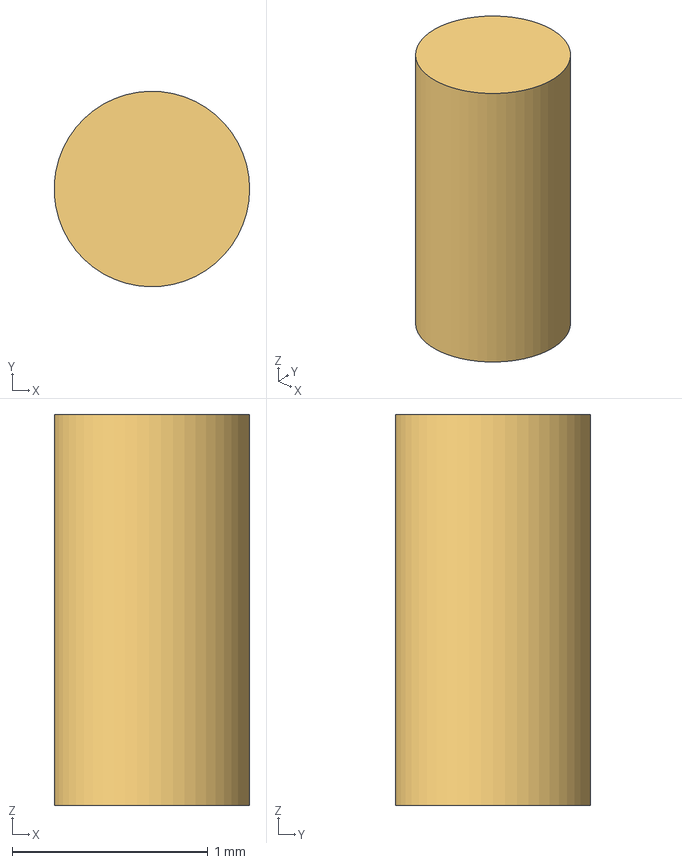
[picture p78: CAD file, 2024-05-24]
part/pewter_foot1.FCStd
0.999 x 1 x 2.00 mm
