serge-scl/mini-keyboard/part/pewter_foot2.FCStd

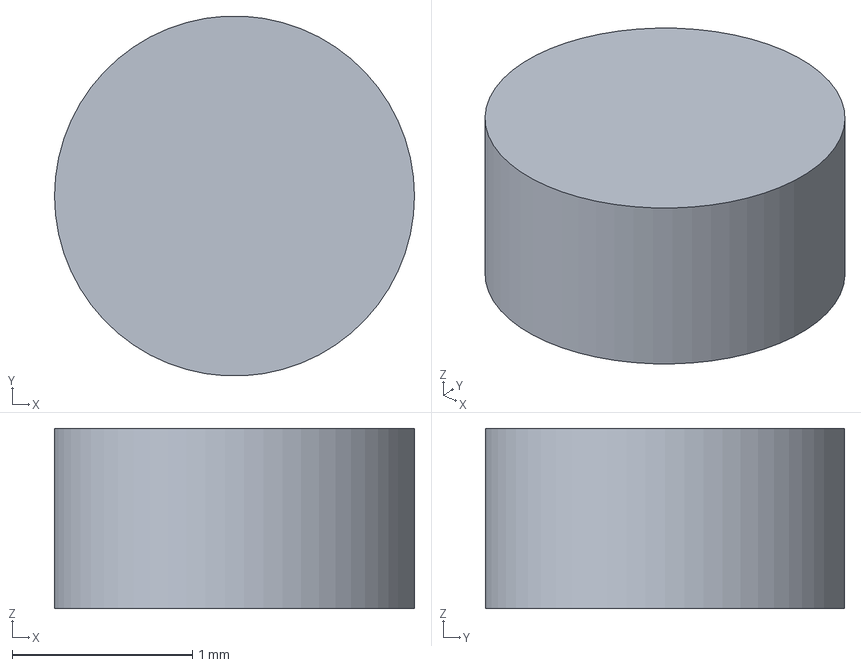
[picture p79: CAD file, 2024-05-24]
part/pewter_foot2.FCStd
2.00 x 2.00 x 1.00 mm
