serge-scl/mini-keyboard/part/magnet_holder.FCStd

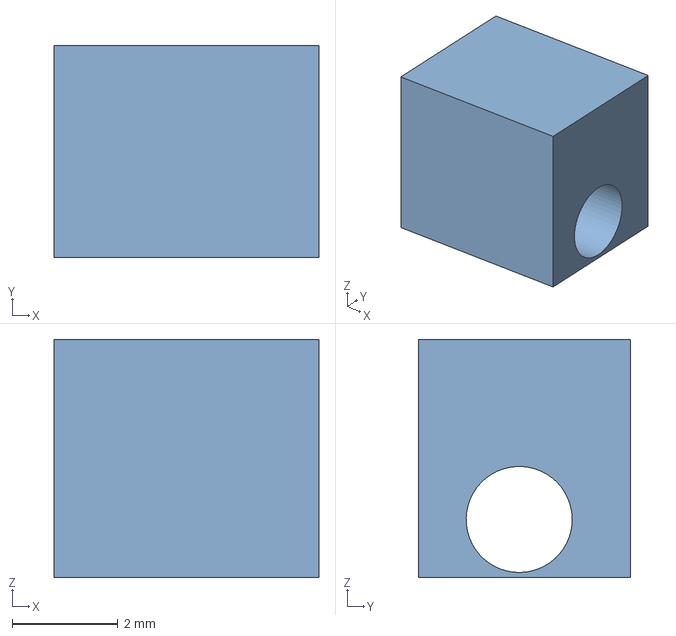
[picture p80: CAD file, 2023-12-05]
part/magnet_holder.FCStd
5.00 x 4.00 x 4.50 mm
