serge-scl/mini-keyboard/part/back_cover.FCStd

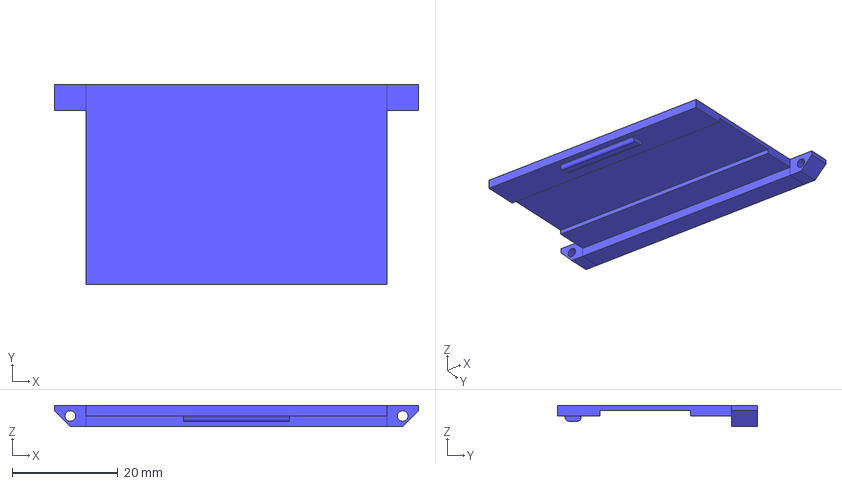
[picture p81: CAD file, 2023-08-21]
part/back_cover.FCStd
69.0 x 38.0 x 4.00 mm
