serge-scl/mini-keyboard/part/stock.FCStd

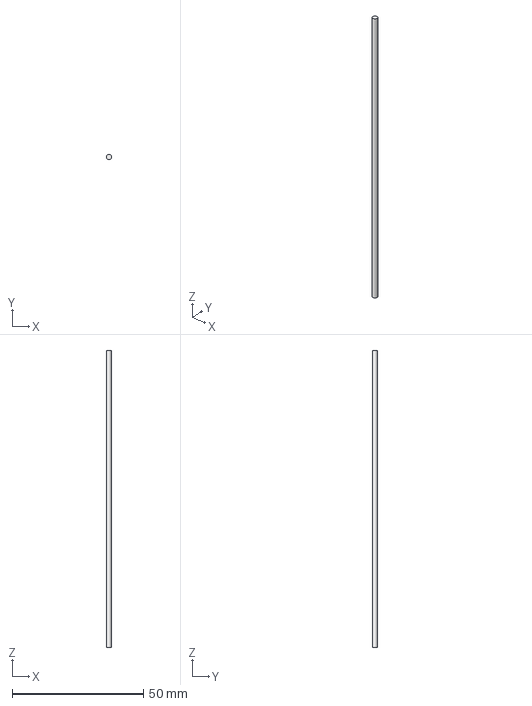
[picture p82: CAD file, 2023-08-03]
part/stock.FCStd
2.00 x 2.00 x 113.0 mm
