serge-scl/mini-keyboard/part/back_lock.FCStd

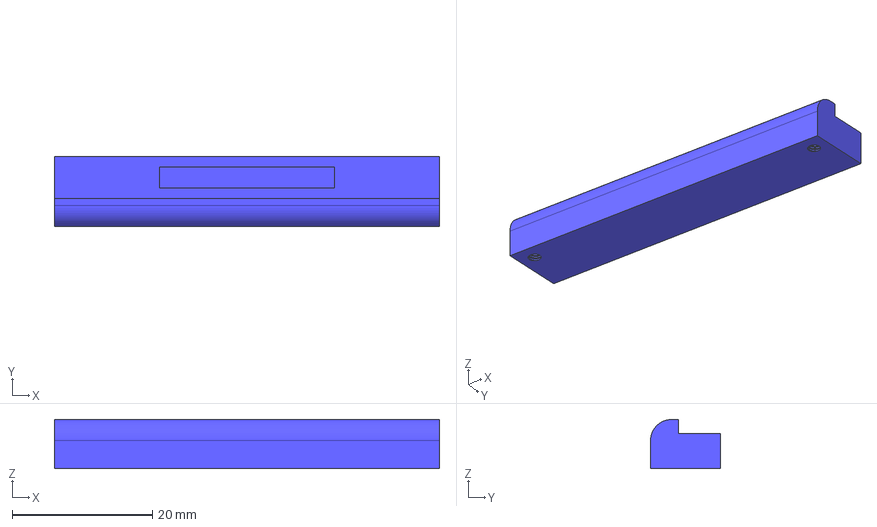
[picture p83: CAD file, 2023-08-03]
part/back_lock.FCStd
55.0 x 10.0 x 7.00 mm
