serge-scl/mini-keyboard/part/axle_tube_case.FCStd

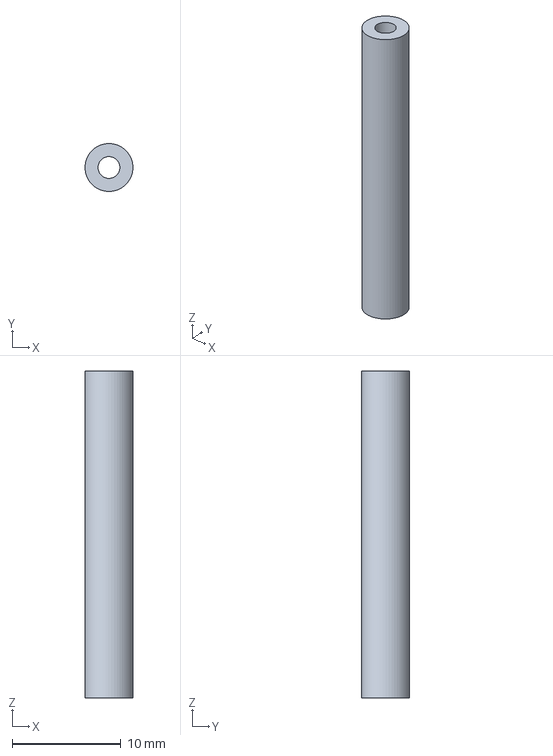
[picture p84: CAD file, 2023-04-01]
part/axle_tube_case.FCStd
4.40 x 4.40 x 30.0 mm
