serge-scl/mini-keyboard/part/fixing_pin.FCStd

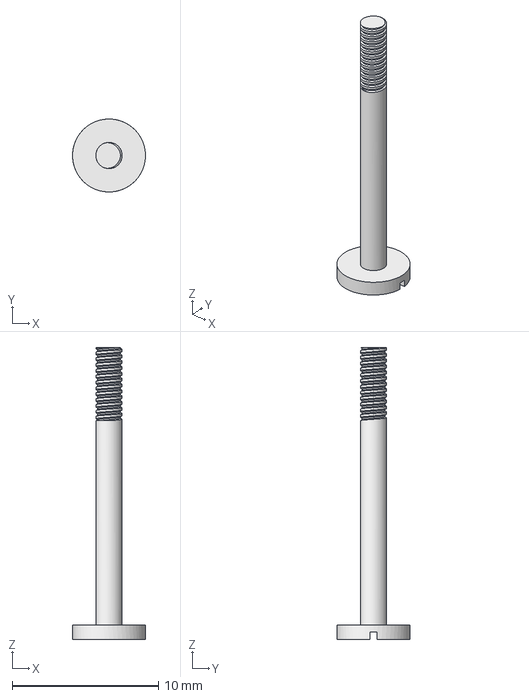
[picture p85: CAD file, 2023-03-29]
part/fixing_pin.FCStd
5.00 x 5.00 x 20.0 mm
