serge-scl/mini-keyboard/part/magnet.FCStd

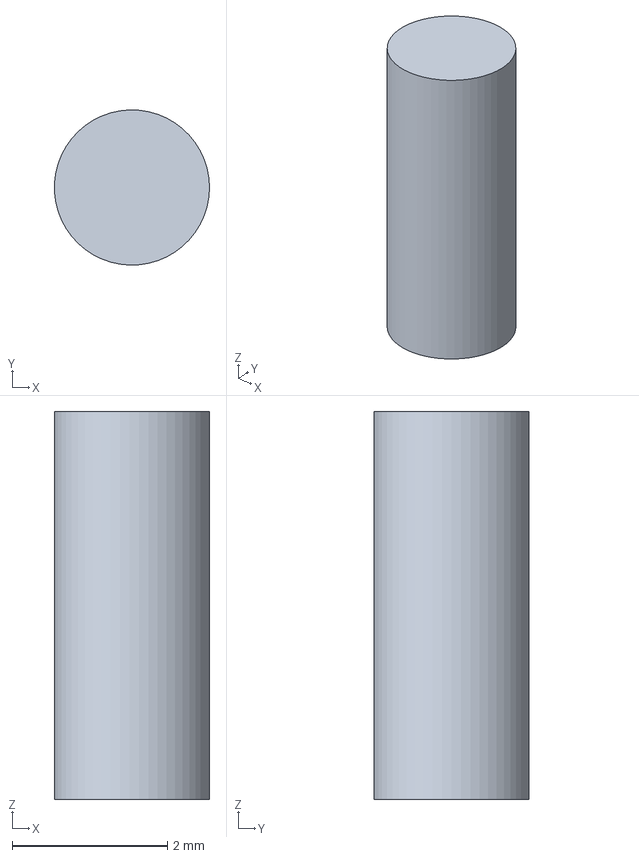
[picture p86: CAD file, 2023-03-29]
part/magnet.FCStd
2.00 x 2.00 x 5.00 mm
