serge-scl/mini-keyboard/part/pewter_conn2.FCStd

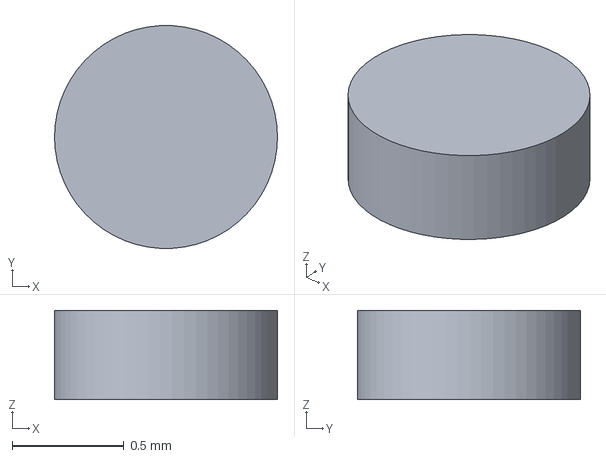
[picture p87: CAD file, 2023-03-26]
part/pewter_conn2.FCStd
1.00 x 0.999 x 0.4 mm
